mosfet05/Metering_Unit/Kicad/Sub_Ethernet.kicad_sch

## KiCad design Kicad/Sub_Ethernet.kicad_sch (2025-03-12)

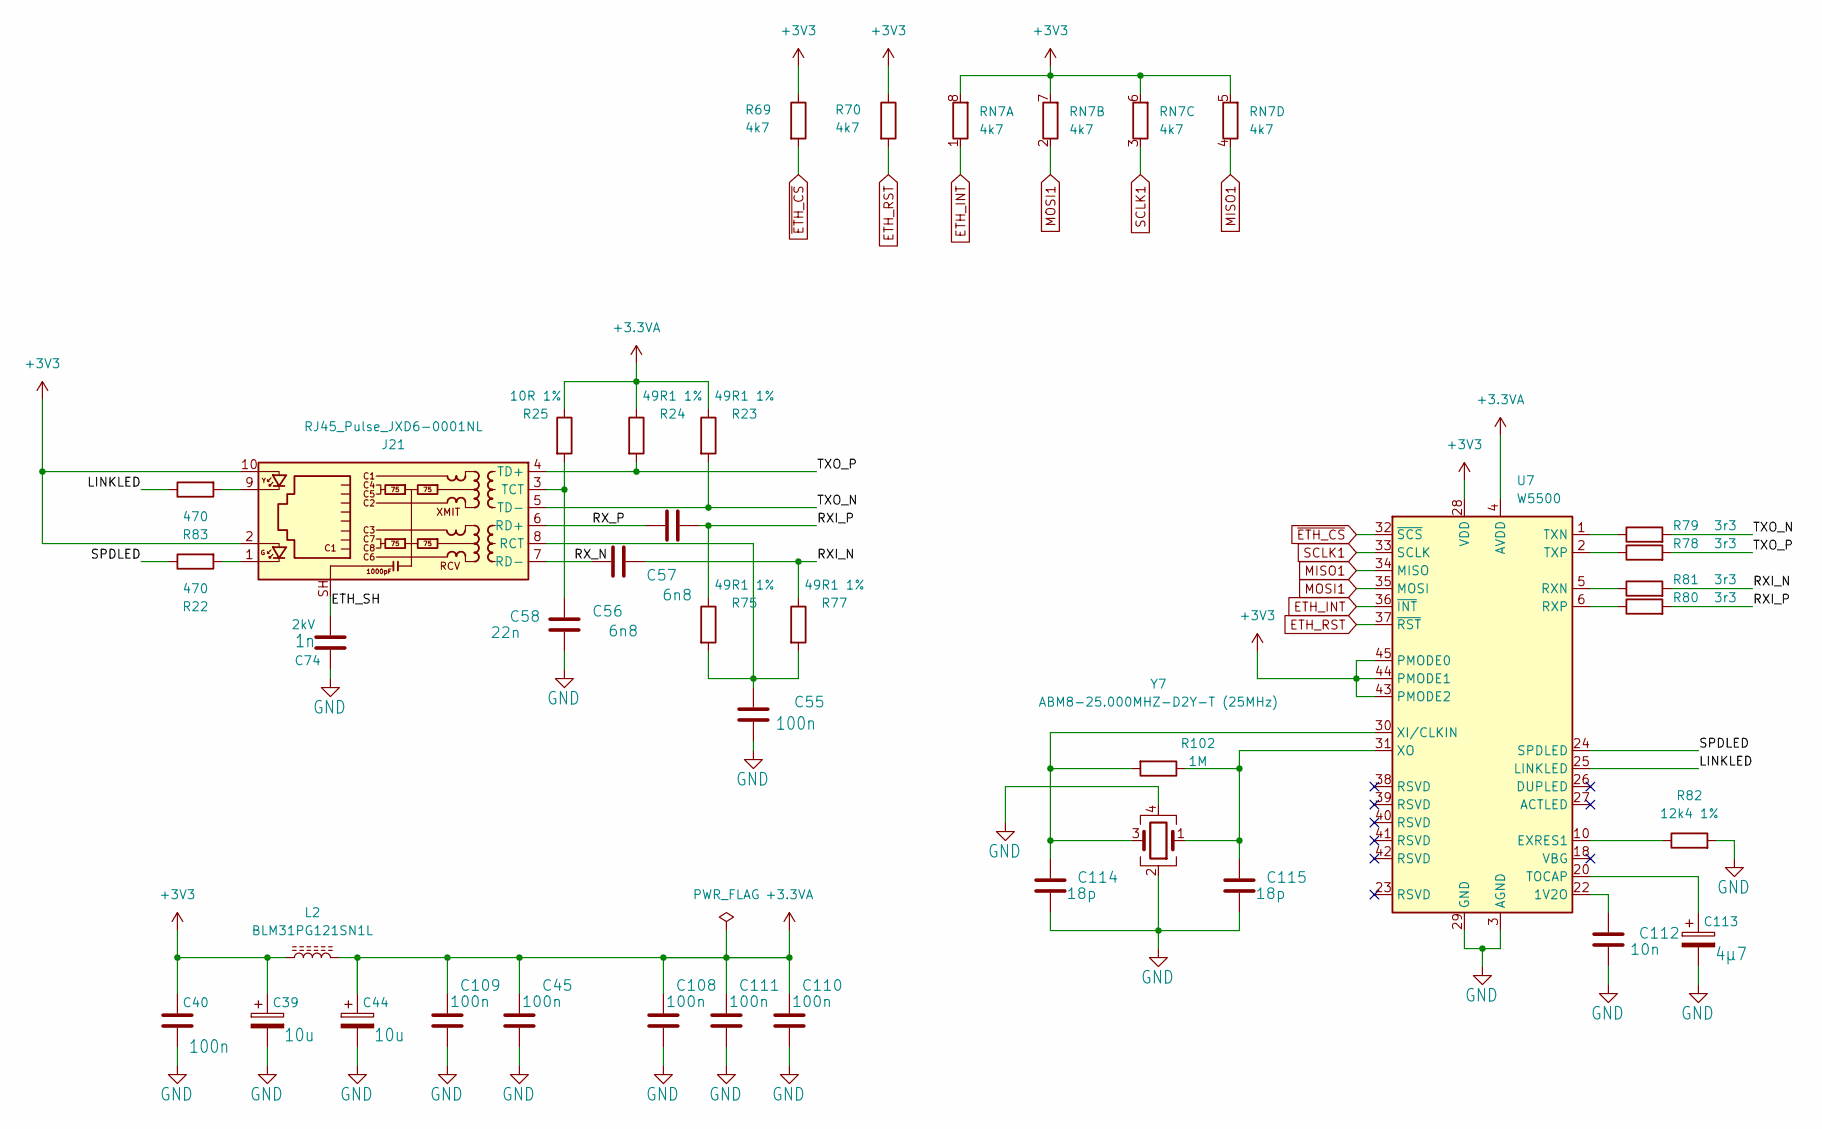
[picture p14: schematic Sub_Ethernet.kicad_sch]

Parts:
C39, C44: 10u; CP_Elec_4x5.3
C40, C55: 100n; C_1210_3225Metric_Pad1.33x2.70mm_HandSolder
C45, C108, C109, C110, C111: 100n; C_0805_2012Metric_Pad1.18x1.45mm_HandSolder
C56, C57: 6n8; C_0805_2012Metric_Pad1.18x1.45mm_HandSolder
C58: 22n; C_0805_2012Metric_Pad1.18x1.45mm_HandSolder
C74: 1n; C_1808_4520Metric_Pad1.72x2.30mm_HandSolder
C112: 10n; C_0805_2012Metric_Pad1.18x1.45mm_HandSolder
C113: 4µ7; CP_Elec_4x5.4
C114, C115: 18p; C_0805_2012Metric_Pad1.18x1.45mm_HandSolder
J21: RJ45_Pulse_JXD6-0001NL; RJ45_Pulse_JXD6-0001NL_Horizontal
L2: BLM31PG121SN1L; L_1206_3216Metric_Pad1.22x1.90mm_HandSolder
R22, R83: 470; R_1210_3225Metric_Pad1.30x2.65mm_HandSolder
R23, R24, R75, R77: 49R1 1%; R_0805_2012Metric_Pad1.20x1.40mm_HandSolder
R25: 10R 1%; R_0805_2012Metric_Pad1.20x1.40mm_HandSolder
R69, R70: 4k7; R_1210_3225Metric_Pad1.30x2.65mm_HandSolder
R78, R79, R80, R81: 3r3; R_0805_2012Metric_Pad1.20x1.40mm_HandSolder
R82: 12k4 1%; R_1210_3225Metric_Pad1.30x2.65mm_HandSolder
R102: 1M; R_0805_2012Metric_Pad1.20x1.40mm_HandSolder
RN7: 4k7; R_Array_Convex_4x1206
U7: W5500; LQFP-48_7x7mm_P0.5mm
Y7: ABM8-25.000MHZ-D2Y-T (25MHz); Crystal_SMD_3225-4Pin_3.2x2.5mm

Connections:
+3.3VA: C44.1, C45.2, C108.2, C109.2, C110.2, C111.2, L2.2, R23.1, R24.1, R25.1, U7.4 (AVDD), U7.8 (AVDD), U7.11 (AVDD), U7.15 (AVDD), U7.17 (AVDD), U7.21 (AVDD)
+3V3: C39.1, C40.1, J21.2, J21.10, L2.1, R69.1, R70.1, RN7.5 (R4.2), RN7.6 (R3.2), RN7.7 (R2.2), RN7.8 (R1.2), U7.28 (VDD), U7.43 (PMODE2), U7.44 (PMODE1), U7.45 (PMODE0)
ETH_INT: RN7.1 (R1.1), U7.36 (~INT)
ETH_RST: R70.2, U7.37 (~RST)
ETH_SH: C74.1, J21.SH
GND: C39.2, C40.2, C44.2, C45.1, C55.1, C58.1, C74.2, C108.1, C109.1, C110.1, C111.1, C112.1, C113.2, C114.1, C115.1, R82.2, U7.3 (AGND), U7.9 (AGND), U7.14 (AGND), U7.16 (AGND), U7.19 (AGND), U7.29 (GND), U7.48 (AGND), Y7.2, Y7.4
LINKLED: R83.1, U7.25 (LINKLED)
MISO1: RN7.4 (R4.1), U7.34 (MISO)
MOSI1: RN7.2 (R2.1), U7.35 (MOSI)
unnamed: C55.2, J21.8 (RCT), R75.2, R77.2
unnamed: C58.2, J21.3 (TCT), R25.2
unnamed: C112.2, U7.22 (1V2O)
unnamed: C113.1, U7.20 (TOCAP)
unnamed: C114.2, R102.2, U7.30 (XI/CLKIN), Y7.3
unnamed: C115.2, R102.1, U7.31 (XO), Y7.1
unnamed: J21.1, R22.2
unnamed: J21.9, R83.2
unnamed: R78.1, U7.2 (TXP)
unnamed: R79.1, U7.1 (TXN)
unnamed: R80.1, U7.6 (RXP)
unnamed: R81.1, U7.5 (RXN)
unnamed: R82.1, U7.10 (EXRES1)
RXI_N: C56.1, R77.1, R81.2
RXI_P: C57.1, R75.1, R80.2
RX_N: C56.2, J21.7 (RD-)
RX_P: C57.2, J21.6 (RD+)
SCLK1: RN7.3 (R3.1), U7.33 (SCLK)
SPDLED: R22.1, U7.24 (SPDLED)
TXO_N: J21.5 (TD-), R23.2, R79.2
TXO_P: J21.4 (TD+), R24.2, R78.2
~ETH_CS: R69.2, U7.32 (~SCS)
