mosfet05/Metering_Unit/Kicad/Sub_IHM.kicad_sch

## KiCad design Kicad/Sub_IHM.kicad_sch (2025-03-12)

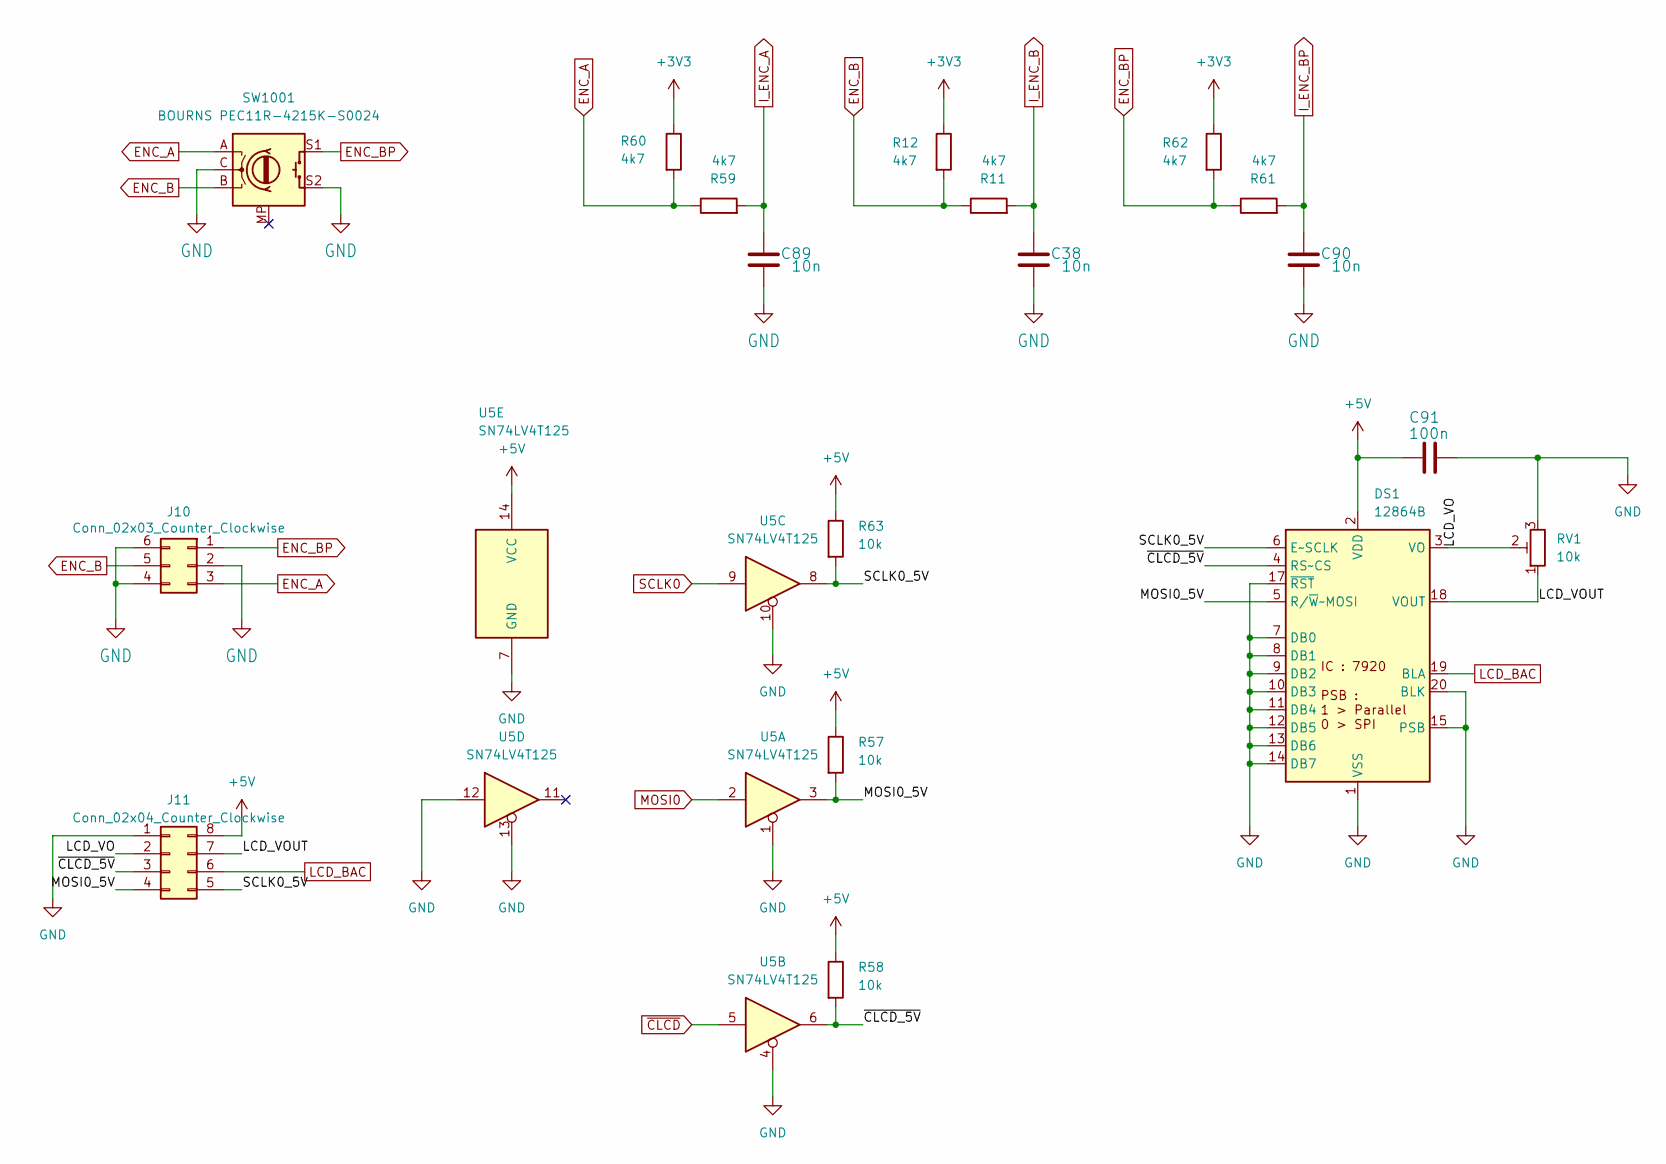
[picture p15: schematic Sub_IHM.kicad_sch]

Parts:
C38, C89, C90: 10n; C_1812_4532Metric_Pad1.57x3.40mm_HandSolder
C91: 100n; C_1812_4532Metric_Pad1.57x3.40mm_HandSolder
DS1: 12864B; GraphicLCD_12864B_WithoutPads
J10: Conn_02x03_Counter_Clockwise; IDC-Header_2x03_P2.54mm_Vertical
J11: Conn_02x04_Counter_Clockwise; IDC-Header_2x04_P2.54mm_Vertical
R11, R12, R59, R60, R61, R62: 4k7; R_1210_3225Metric_Pad1.30x2.65mm_HandSolder
R57, R58, R63: 10k; R_1210_3225Metric_Pad1.30x2.65mm_HandSolder
RV1: 10k; Potentiometer_Piher_T-16H_Single_Horizontal
SW1001: BOURNS PEC11R-4215K-S0024
U5: SN74LV4T125; TSSOP-14_4.4x5mm_P0.65mm

Connections:
+3V3: R12.1, R60.1, R62.1
+5V: C91.1, DS1.2 (VDD), J11.8, R57.1, R58.1, R63.1, U5.14 (VCC)
ENC_A: J10.3, R59.1, R60.2, SW1001.A
ENC_B: J10.5, R11.1, R12.2, SW1001.B
ENC_BP: J10.1, R61.1, R62.2, SW1001.S1
GND: C38.2, C89.2, C90.2, C91.2, DS1.1 (VSS), DS1.7 (DB0), DS1.8 (DB1), DS1.9 (DB2), DS1.10 (DB3), DS1.11 (DB4), DS1.12 (DB5), DS1.13 (DB6), DS1.14 (DB7), DS1.15 (PSB), DS1.17 (~RST), DS1.20 (BLK), J10.2, J10.4, J10.6, J11.1, RV1.3, SW1001.C, SW1001.S2, U5.1, U5.4, U5.7 (GND), U5.10, U5.12, U5.13
I_ENC_A: C89.1, R59.2
I_ENC_B: C38.1, R11.2
I_ENC_BP: C90.1, R61.2
LCD_BAC: DS1.19 (BLA), J11.6
LCD_VO: DS1.3 (VO), J11.2, RV1.2
LCD_VOUT: DS1.18 (NC), J11.7, RV1.1
MOSI0: U5.2
MOSI0_5V: DS1.5 (R/~W~MOSI), J11.4, R57.2, U5.3
SCLK0: U5.9
SCLK0_5V: DS1.6 (E~SCLK), J11.5, R63.2, U5.8
~CLCD_5V: DS1.4 (RS~CS), J11.3, R58.2, U5.6
~CLCD: U5.5
