mosfet05/Metering_Unit/Kicad/Sub_Mes_01.kicad_sch

## KiCad design Kicad/Sub_Mes_01.kicad_sch (2025-03-12)

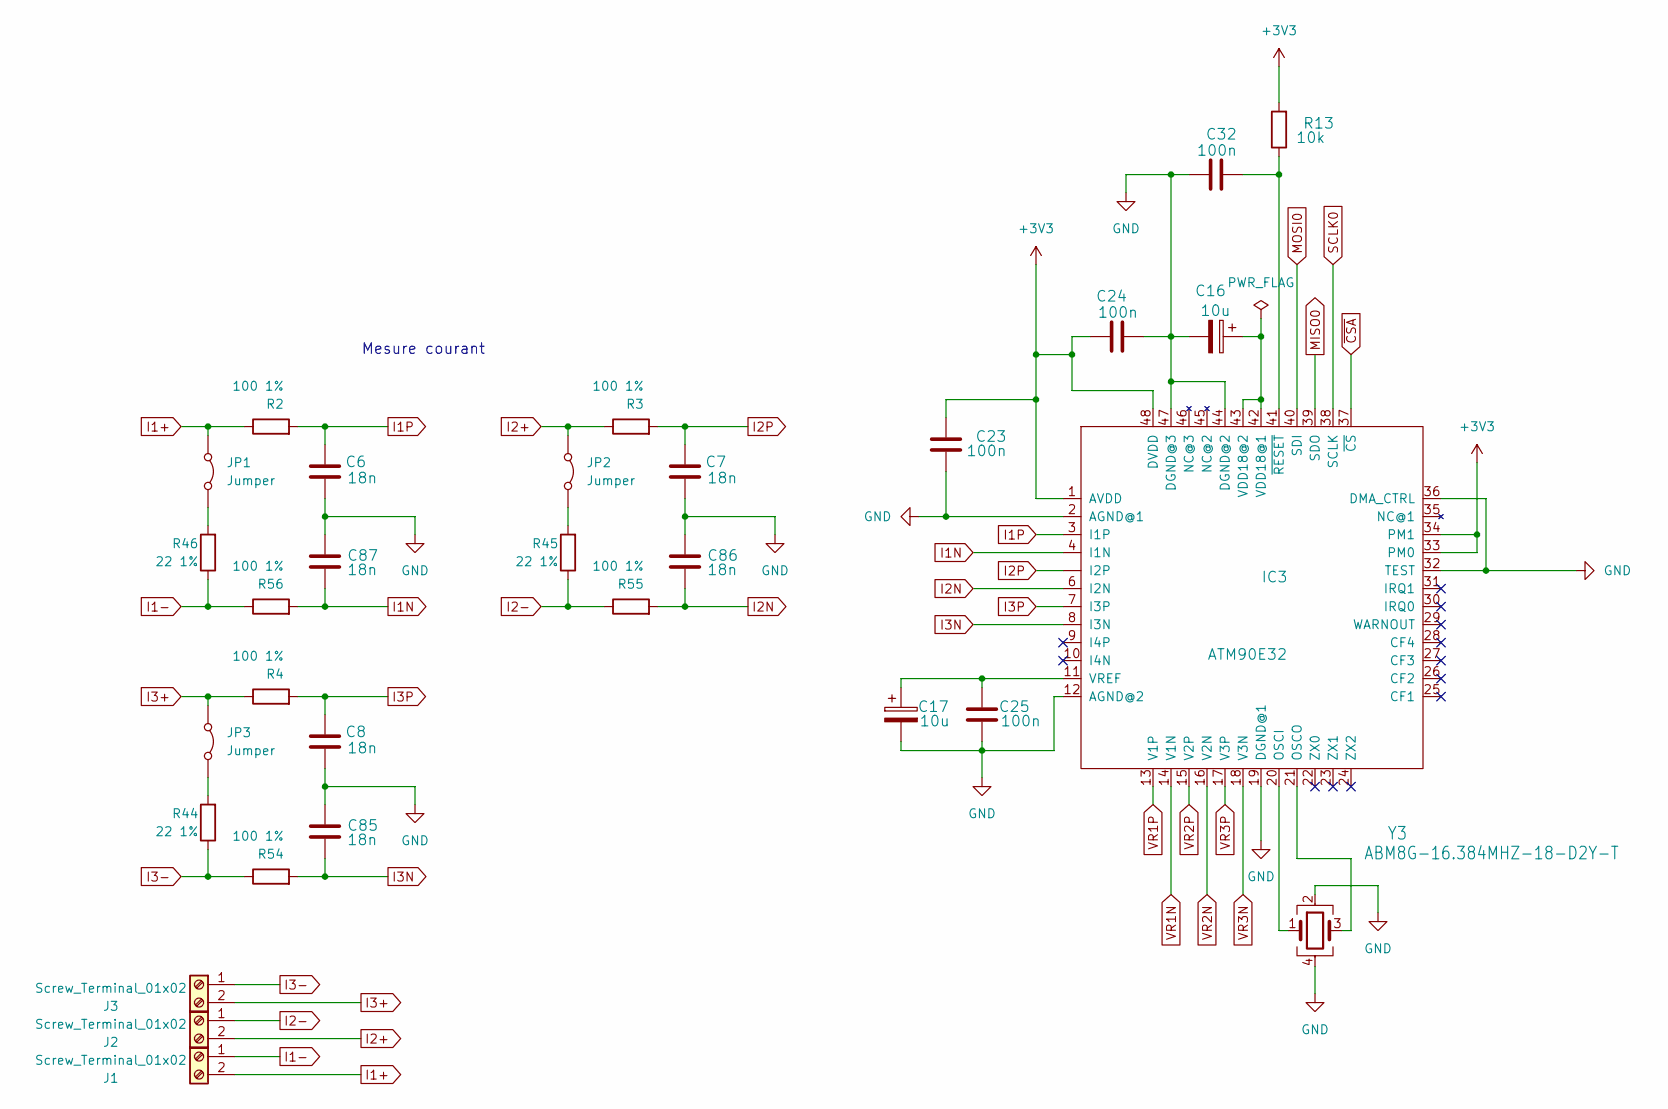
[picture p16: schematic Sub_Mes_01.kicad_sch]

Parts:
C6, C7, C8, C85, C86, C87: 18n; C_0805_2012Metric_Pad1.18x1.45mm_HandSolder
C16, C17: 10u; CP_Elec_4x5.3
C23, C24, C25, C32: 100n; C_1812_4532Metric_Pad1.57x3.40mm_HandSolder
IC3: ATM90E32; TQFP-48_7x7mm_P0.5mm
J1, J2, J3: Screw_Terminal_01x02; TerminalBlock_VN_1x02_P2.54mm_Horizontal
JP1, JP2, JP3: Jumper; PinHeader_1x02_P2.54mm_Vertical
R2, R3, R4, R54, R55, R56: 100 1%; R_1210_3225Metric_Pad1.30x2.65mm_HandSolder
R13: 10k; R_1210_3225Metric_Pad1.30x2.65mm_HandSolder
R44, R45, R46: 22 1%; R_1210_3225Metric_Pad1.30x2.65mm_HandSolder
Y3: ABM8G-16.384MHZ-18-D2Y-T; Crystal_SMD_3225-4Pin_3.2x2.5mm

Connections:
+3V3: C23.2, C24.2, IC3.1 (AVDD), IC3.33 (PM0), IC3.34 (PM1), IC3.48 (DVDD), R13.2
GND: C6.2, C7.2, C8.2, C16.2, C17.2, C23.1, C24.1, C25.2, C32.2, C85.1, C86.1, C87.1, IC3.2 (AGND@1), IC3.12 (AGND@2), IC3.19 (DGND@1), IC3.32 (TEST), IC3.36 (DMA_CTRL), IC3.44 (DGND@2), IC3.47 (DGND@3), Y3.2, Y3.4
I1+: J1.2, JP1.1 (A), R2.1
I1-: J1.1, R46.1, R56.1
I1N: C87.2, IC3.4 (I1N), R56.2
I1P: C6.1, IC3.3 (I1P), R2.2
I2+: J2.2, JP2.1 (A), R3.1
I2-: J2.1, R45.1, R55.1
I2N: C86.2, IC3.6 (I2N), R55.2
I2P: C7.1, IC3.5 (I2P), R3.2
I3+: J3.2, JP3.1 (A), R4.1
I3-: J3.1, R44.1, R54.1
I3N: C85.2, IC3.8 (I3N), R54.2
I3P: C8.1, IC3.7 (I3P), R4.2
MISO0: IC3.39 (SDO)
MOSI0: IC3.40 (SDI)
unnamed: C16.1, IC3.42 (VDD18@1), IC3.43 (VDD18@2)
unnamed: C17.1, C25.1, IC3.11 (VREF)
unnamed: C32.1, IC3.41 (~RESET), R13.1
unnamed: IC3.20 (OSCI), Y3.1
unnamed: IC3.21 (OSCO), Y3.3
unnamed: JP1.2 (B), R46.2
unnamed: JP2.2 (B), R45.2
unnamed: JP3.2 (B), R44.2
SCLK0: IC3.38 (SCLK)
VR1N: IC3.14 (V1N)
VR1P: IC3.13 (V1P)
VR2N: IC3.16 (V2N)
VR2P: IC3.15 (V2P)
VR3N: IC3.18 (V3N)
VR3P: IC3.17 (V3P)
~CSA: IC3.37 (~CS)

Notes on the sheet:
Mesure courant
