mosfet05/Metering_Unit/Kicad/Sub_Mes_02.kicad_sch

## KiCad design Kicad/Sub_Mes_02.kicad_sch (2025-03-12)

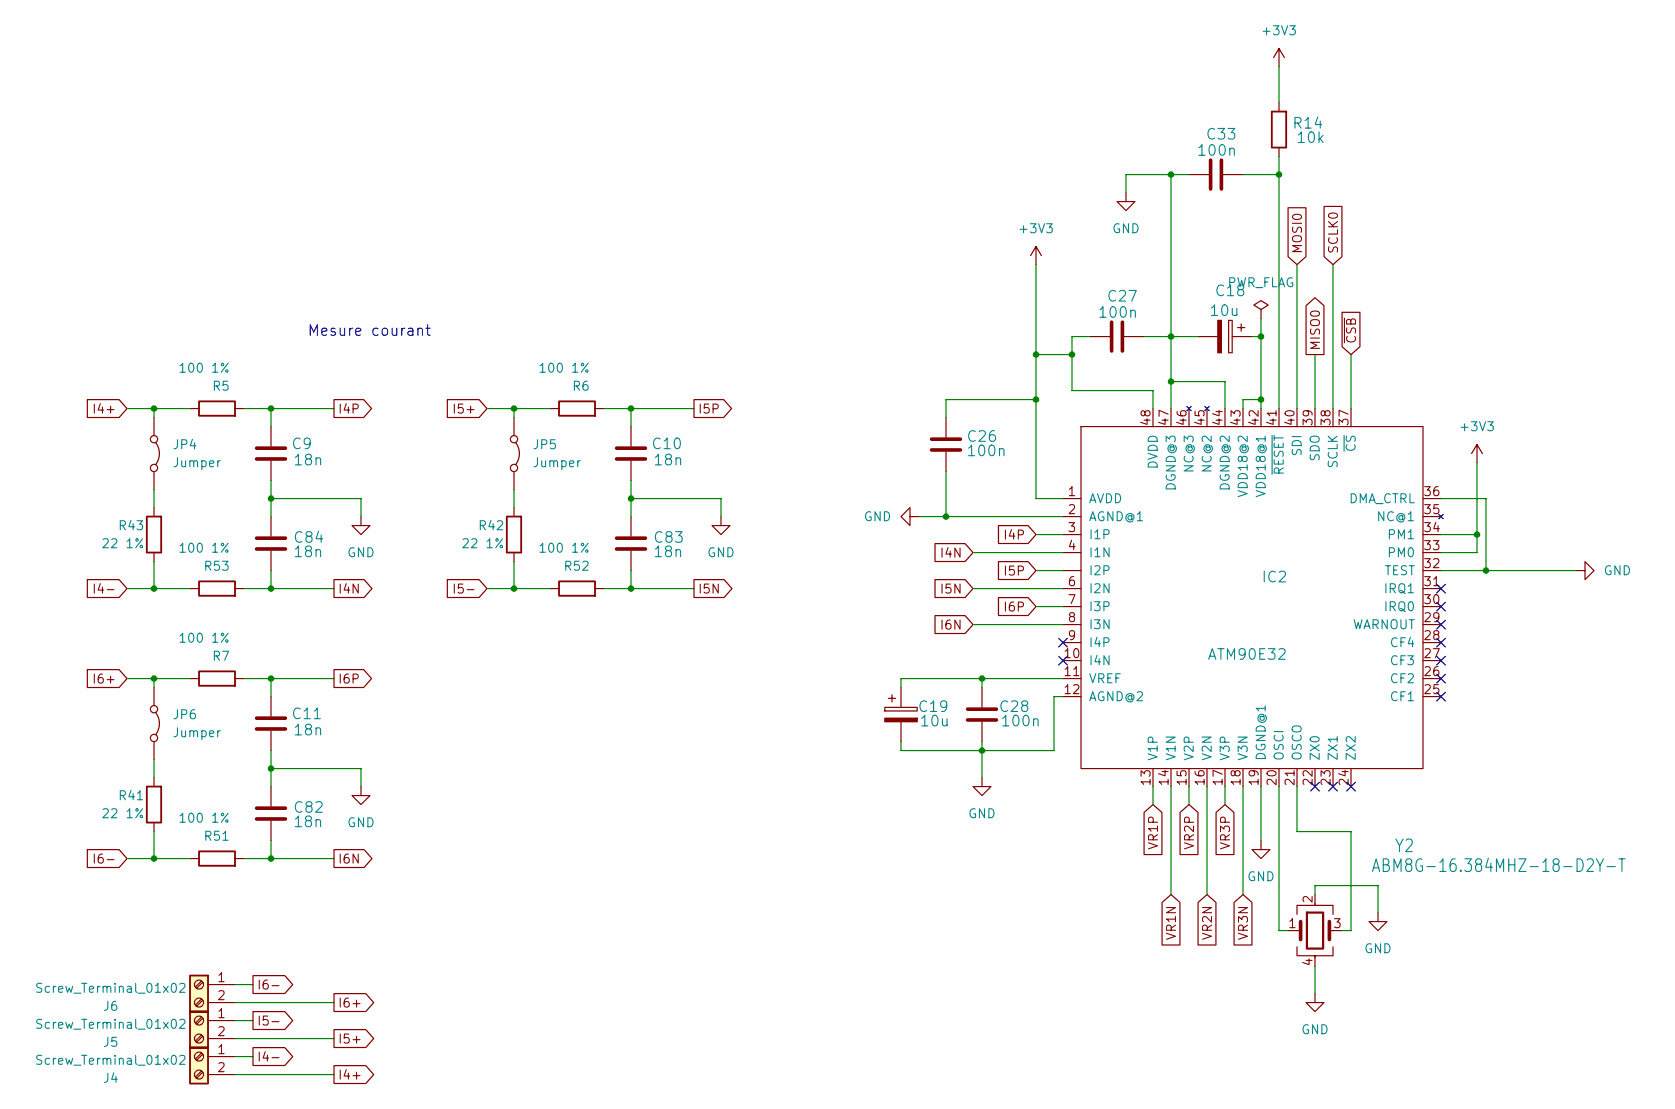
[picture p17: schematic Sub_Mes_02.kicad_sch]

Parts:
C9, C10, C11, C82, C83, C84: 18n; C_0805_2012Metric_Pad1.18x1.45mm_HandSolder
C18, C19: 10u; CP_Elec_4x5.3
C26, C27, C28, C33: 100n; C_1812_4532Metric_Pad1.57x3.40mm_HandSolder
IC2: ATM90E32; TQFP-48_7x7mm_P0.5mm
J4, J5, J6: Screw_Terminal_01x02; TerminalBlock_VN_1x02_P2.54mm_Horizontal
JP4, JP5, JP6: Jumper; PinHeader_1x02_P2.54mm_Vertical
R5, R6, R7, R51, R52, R53: 100 1%; R_1210_3225Metric_Pad1.30x2.65mm_HandSolder
R14: 10k; R_1210_3225Metric_Pad1.30x2.65mm_HandSolder
R41, R42, R43: 22 1%; R_1210_3225Metric_Pad1.30x2.65mm_HandSolder
Y2: ABM8G-16.384MHZ-18-D2Y-T; Crystal_SMD_3225-4Pin_3.2x2.5mm

Connections:
+3V3: C26.2, C27.2, IC2.1 (AVDD), IC2.33 (PM0), IC2.34 (PM1), IC2.48 (DVDD), R14.2
GND: C9.2, C10.2, C11.2, C18.2, C19.2, C26.1, C27.1, C28.2, C33.2, C82.1, C83.1, C84.1, IC2.2 (AGND@1), IC2.12 (AGND@2), IC2.19 (DGND@1), IC2.32 (TEST), IC2.36 (DMA_CTRL), IC2.44 (DGND@2), IC2.47 (DGND@3), Y2.2, Y2.4
I4+: J4.2, JP4.1 (A), R5.1
I4-: J4.1, R43.1, R53.1
I4N: C84.2, IC2.4 (I1N), R53.2
I4P: C9.1, IC2.3 (I1P), R5.2
I5+: J5.2, JP5.1 (A), R6.1
I5-: J5.1, R42.1, R52.1
I5N: C83.2, IC2.6 (I2N), R52.2
I5P: C10.1, IC2.5 (I2P), R6.2
I6+: J6.2, JP6.1 (A), R7.1
I6-: J6.1, R41.1, R51.1
I6N: C82.2, IC2.8 (I3N), R51.2
I6P: C11.1, IC2.7 (I3P), R7.2
MISO0: IC2.39 (SDO)
MOSI0: IC2.40 (SDI)
unnamed: C18.1, IC2.42 (VDD18@1), IC2.43 (VDD18@2)
unnamed: C19.1, C28.1, IC2.11 (VREF)
unnamed: C33.1, IC2.41 (~RESET), R14.1
unnamed: IC2.20 (OSCI), Y2.1
unnamed: IC2.21 (OSCO), Y2.3
unnamed: JP4.2 (B), R43.2
unnamed: JP5.2 (B), R42.2
unnamed: JP6.2 (B), R41.2
SCLK0: IC2.38 (SCLK)
VR1N: IC2.14 (V1N)
VR1P: IC2.13 (V1P)
VR2N: IC2.16 (V2N)
VR2P: IC2.15 (V2P)
VR3N: IC2.18 (V3N)
VR3P: IC2.17 (V3P)
~CSB: IC2.37 (~CS)

Notes on the sheet:
Mesure courant
