mosfet05/Metering_Unit/Kicad/Sub_Mes_03.kicad_sch

## KiCad design Kicad/Sub_Mes_03.kicad_sch (2025-03-12)

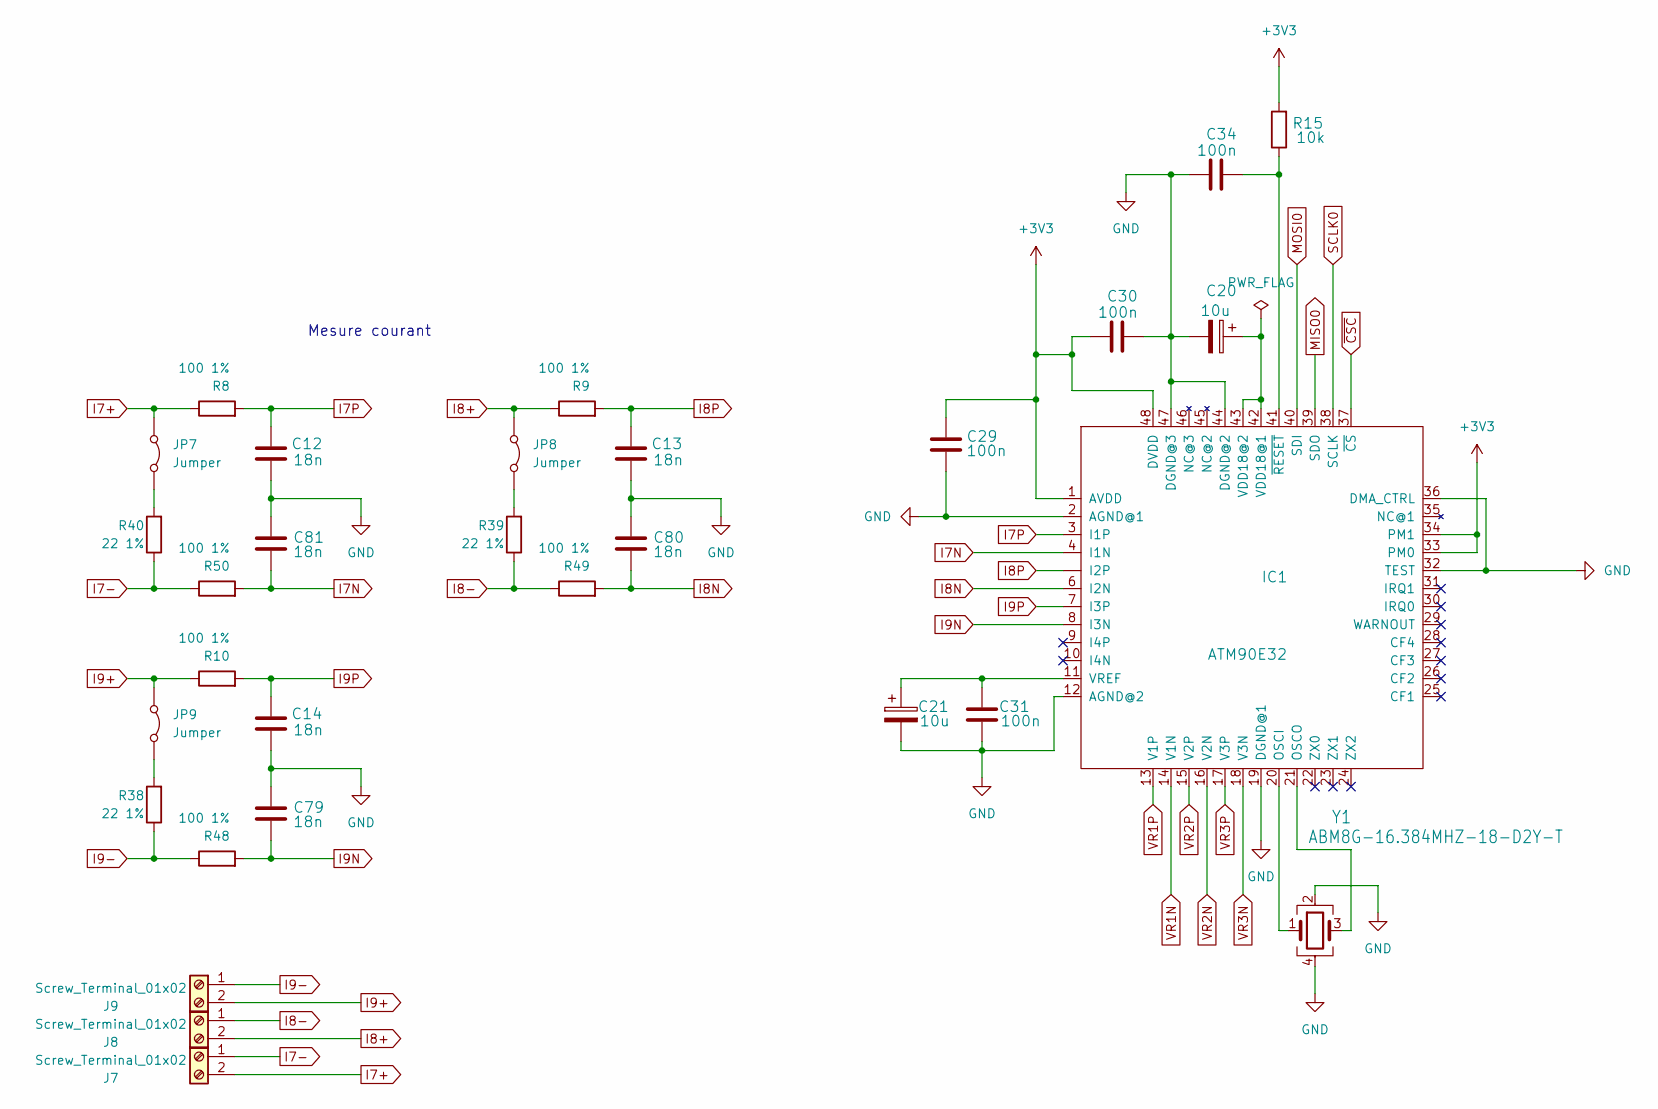
[picture p18: schematic Sub_Mes_03.kicad_sch]

Parts:
C12, C13, C14, C79, C80, C81: 18n; C_0805_2012Metric_Pad1.18x1.45mm_HandSolder
C20, C21: 10u; CP_Elec_4x5.3
C29, C30, C31, C34: 100n; C_1812_4532Metric_Pad1.57x3.40mm_HandSolder
IC1: ATM90E32; TQFP-48_7x7mm_P0.5mm
J7, J8, J9: Screw_Terminal_01x02; TerminalBlock_VN_1x02_P2.54mm_Horizontal
JP7, JP8, JP9: Jumper; PinHeader_1x02_P2.54mm_Vertical
R8, R9, R10, R48, R49, R50: 100 1%; R_1210_3225Metric_Pad1.30x2.65mm_HandSolder
R15: 10k; R_1210_3225Metric_Pad1.30x2.65mm_HandSolder
R38, R39, R40: 22 1%; R_1210_3225Metric_Pad1.30x2.65mm_HandSolder
Y1: ABM8G-16.384MHZ-18-D2Y-T; Crystal_SMD_3225-4Pin_3.2x2.5mm

Connections:
+3V3: C29.2, C30.2, IC1.1 (AVDD), IC1.33 (PM0), IC1.34 (PM1), IC1.48 (DVDD), R15.2
GND: C12.2, C13.2, C14.2, C20.2, C21.2, C29.1, C30.1, C31.2, C34.2, C79.1, C80.1, C81.1, IC1.2 (AGND@1), IC1.12 (AGND@2), IC1.19 (DGND@1), IC1.32 (TEST), IC1.36 (DMA_CTRL), IC1.44 (DGND@2), IC1.47 (DGND@3), Y1.2, Y1.4
I7+: J7.2, JP7.1 (A), R8.1
I7-: J7.1, R40.1, R50.1
I7N: C81.2, IC1.4 (I1N), R50.2
I7P: C12.1, IC1.3 (I1P), R8.2
I8+: J8.2, JP8.1 (A), R9.1
I8-: J8.1, R39.1, R49.1
I8N: C80.2, IC1.6 (I2N), R49.2
I8P: C13.1, IC1.5 (I2P), R9.2
I9+: J9.2, JP9.1 (A), R10.1
I9-: J9.1, R38.1, R48.1
I9N: C79.2, IC1.8 (I3N), R48.2
I9P: C14.1, IC1.7 (I3P), R10.2
MISO0: IC1.39 (SDO)
MOSI0: IC1.40 (SDI)
unnamed: C20.1, IC1.42 (VDD18@1), IC1.43 (VDD18@2)
unnamed: C21.1, C31.1, IC1.11 (VREF)
unnamed: C34.1, IC1.41 (~RESET), R15.1
unnamed: IC1.20 (OSCI), Y1.1
unnamed: IC1.21 (OSCO), Y1.3
unnamed: JP7.2 (B), R40.2
unnamed: JP8.2 (B), R39.2
unnamed: JP9.2 (B), R38.2
SCLK0: IC1.38 (SCLK)
VR1N: IC1.14 (V1N)
VR1P: IC1.13 (V1P)
VR2N: IC1.16 (V2N)
VR2P: IC1.15 (V2P)
VR3N: IC1.18 (V3N)
VR3P: IC1.17 (V3P)
~CSC: IC1.37 (~CS)

Notes on the sheet:
Mesure courant
