mosfet05/Metering_Unit/Kicad/Sub_Mes_04.kicad_sch

## KiCad design Kicad/Sub_Mes_04.kicad_sch (2025-03-12)

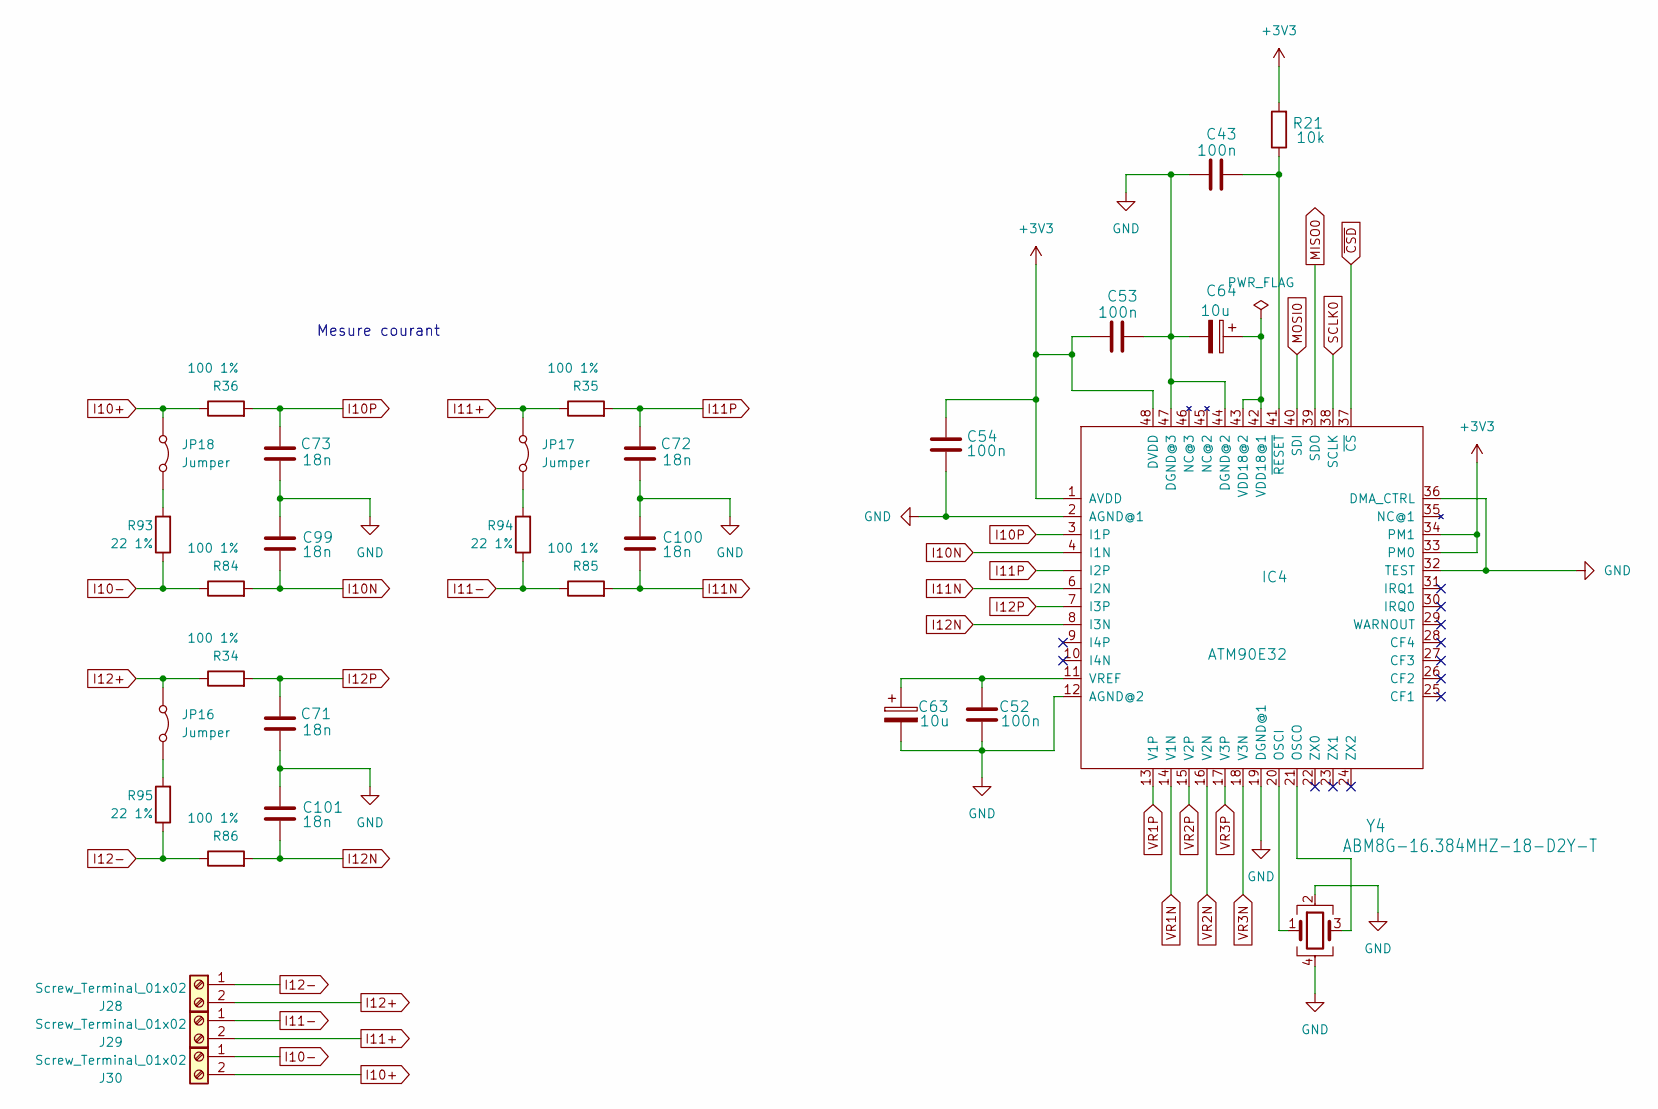
[picture p19: schematic Sub_Mes_04.kicad_sch]

Parts:
C43, C52, C53, C54: 100n; C_1812_4532Metric_Pad1.57x3.40mm_HandSolder
C63, C64: 10u; CP_Elec_4x5.3
C71, C72, C73, C99, C100, C101: 18n; C_0805_2012Metric_Pad1.18x1.45mm_HandSolder
IC4: ATM90E32; TQFP-48_7x7mm_P0.5mm
J28, J29, J30: Screw_Terminal_01x02; TerminalBlock_VN_1x02_P2.54mm_Horizontal
JP16, JP17, JP18: Jumper; PinHeader_1x02_P2.54mm_Vertical
R21: 10k; R_1210_3225Metric_Pad1.30x2.65mm_HandSolder
R34, R35, R36, R84, R85, R86: 100 1%; R_1210_3225Metric_Pad1.30x2.65mm_HandSolder
R93, R94, R95: 22 1%; R_1210_3225Metric_Pad1.30x2.65mm_HandSolder
Y4: ABM8G-16.384MHZ-18-D2Y-T; Crystal_SMD_3225-4Pin_3.2x2.5mm

Connections:
+3V3: C53.2, C54.2, IC4.1 (AVDD), IC4.33 (PM0), IC4.34 (PM1), IC4.48 (DVDD), R21.2
GND: C43.2, C52.2, C53.1, C54.1, C63.2, C64.2, C71.2, C72.2, C73.2, C99.1, C100.1, C101.1, IC4.2 (AGND@1), IC4.12 (AGND@2), IC4.19 (DGND@1), IC4.32 (TEST), IC4.36 (DMA_CTRL), IC4.44 (DGND@2), IC4.47 (DGND@3), Y4.2, Y4.4
I10+: J30.2, JP18.1 (A), R36.1
I10-: J30.1, R84.1, R93.1
I10N: C99.2, IC4.4 (I1N), R84.2
I10P: C73.1, IC4.3 (I1P), R36.2
I11+: J29.2, JP17.1 (A), R35.1
I11-: J29.1, R85.1, R94.1
I11N: C100.2, IC4.6 (I2N), R85.2
I11P: C72.1, IC4.5 (I2P), R35.2
I12+: J28.2, JP16.1 (A), R34.1
I12-: J28.1, R86.1, R95.1
I12N: C101.2, IC4.8 (I3N), R86.2
I12P: C71.1, IC4.7 (I3P), R34.2
MISO0: IC4.39 (SDO)
MOSI0: IC4.40 (SDI)
unnamed: C43.1, IC4.41 (~RESET), R21.1
unnamed: C52.1, C63.1, IC4.11 (VREF)
unnamed: C64.1, IC4.42 (VDD18@1), IC4.43 (VDD18@2)
unnamed: IC4.20 (OSCI), Y4.1
unnamed: IC4.21 (OSCO), Y4.3
unnamed: JP16.2 (B), R95.2
unnamed: JP17.2 (B), R94.2
unnamed: JP18.2 (B), R93.2
SCLK0: IC4.38 (SCLK)
VR1N: IC4.14 (V1N)
VR1P: IC4.13 (V1P)
VR2N: IC4.16 (V2N)
VR2P: IC4.15 (V2P)
VR3N: IC4.18 (V3N)
VR3P: IC4.17 (V3P)
~CSD: IC4.37 (~CS)

Notes on the sheet:
Mesure courant
