mosfet05/Metering_Unit/Kicad/Sub_Mes_05.kicad_sch

## KiCad design Kicad/Sub_Mes_05.kicad_sch (2025-03-12)

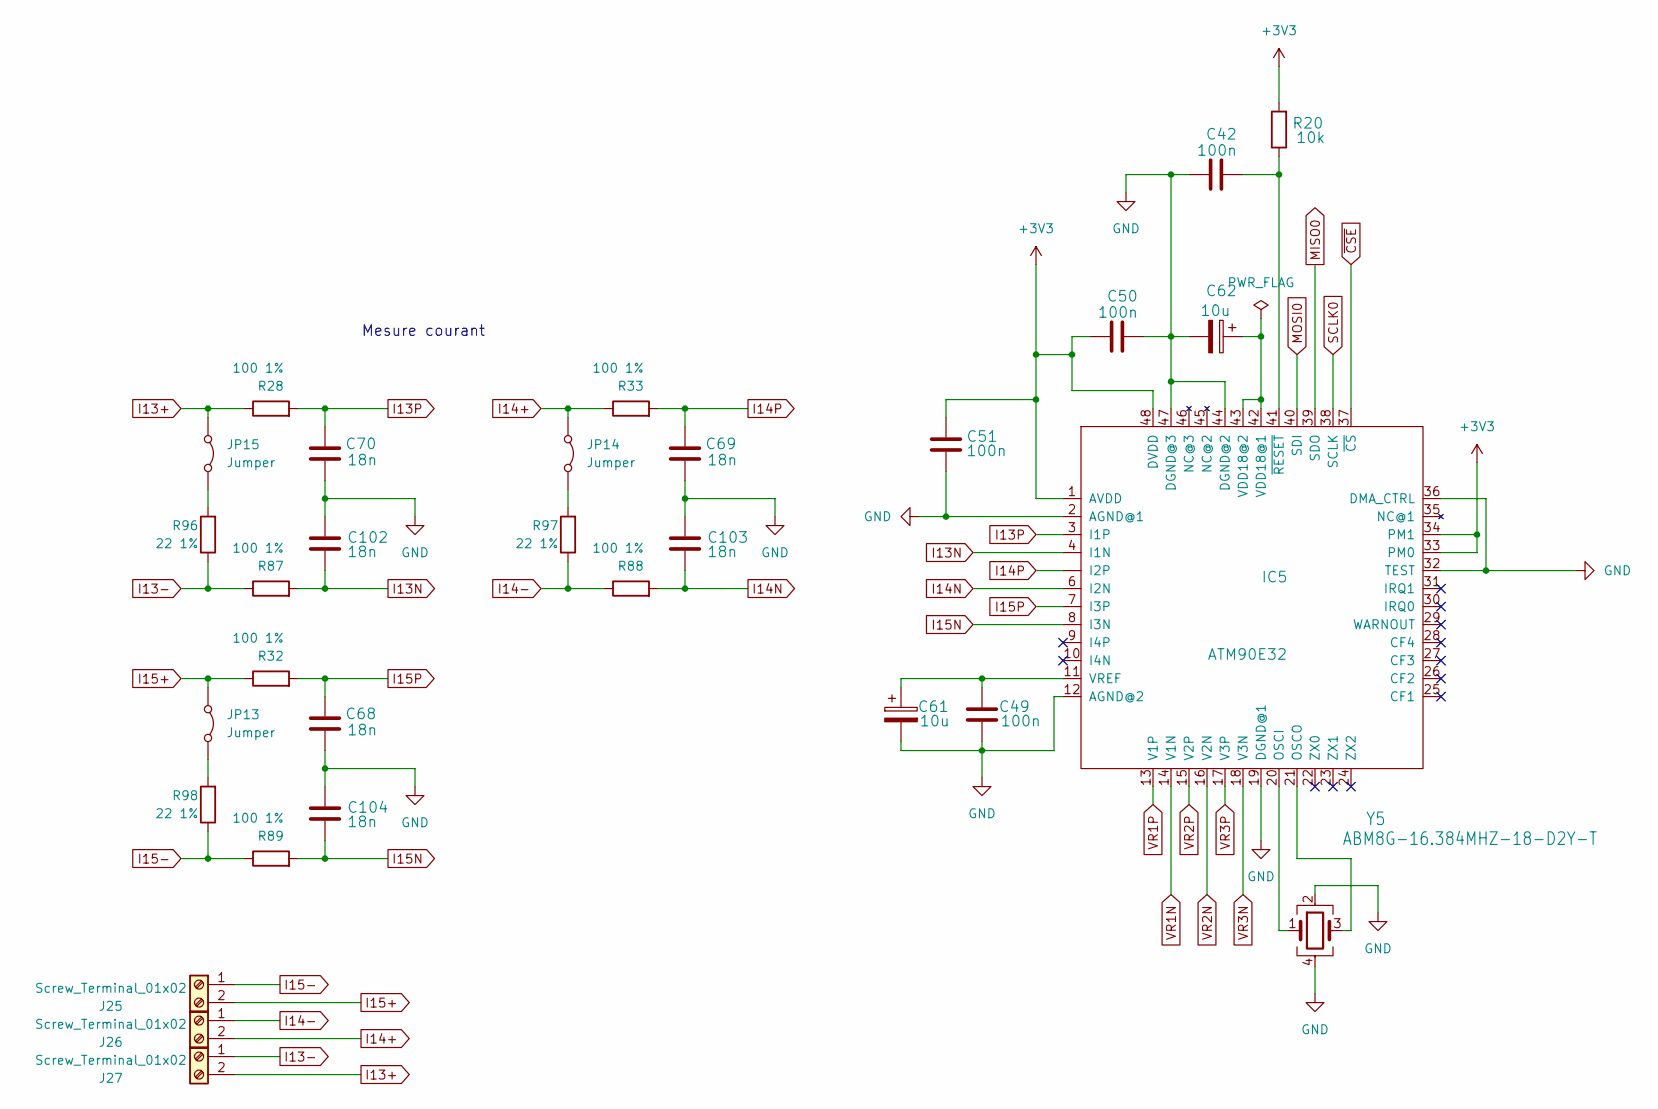
[picture p20: schematic Sub_Mes_05.kicad_sch]

Parts:
C42, C49, C50, C51: 100n; C_1812_4532Metric_Pad1.57x3.40mm_HandSolder
C61, C62: 10u; CP_Elec_4x5.3
C68, C69, C70, C102, C103, C104: 18n; C_0805_2012Metric_Pad1.18x1.45mm_HandSolder
IC5: ATM90E32; TQFP-48_7x7mm_P0.5mm
J25, J26, J27: Screw_Terminal_01x02; TerminalBlock_VN_1x02_P2.54mm_Horizontal
JP13, JP14, JP15: Jumper; PinHeader_1x02_P2.54mm_Vertical
R20: 10k; R_1210_3225Metric_Pad1.30x2.65mm_HandSolder
R28, R32, R33, R87, R88, R89: 100 1%; R_1210_3225Metric_Pad1.30x2.65mm_HandSolder
R96, R97, R98: 22 1%; R_1210_3225Metric_Pad1.30x2.65mm_HandSolder
Y5: ABM8G-16.384MHZ-18-D2Y-T; Crystal_SMD_3225-4Pin_3.2x2.5mm

Connections:
+3V3: C50.2, C51.2, IC5.1 (AVDD), IC5.33 (PM0), IC5.34 (PM1), IC5.48 (DVDD), R20.2
GND: C42.2, C49.2, C50.1, C51.1, C61.2, C62.2, C68.2, C69.2, C70.2, C102.1, C103.1, C104.1, IC5.2 (AGND@1), IC5.12 (AGND@2), IC5.19 (DGND@1), IC5.32 (TEST), IC5.36 (DMA_CTRL), IC5.44 (DGND@2), IC5.47 (DGND@3), Y5.2, Y5.4
I13+: J27.2, JP15.1 (A), R28.1
I13-: J27.1, R87.1, R96.1
I13N: C102.2, IC5.4 (I1N), R87.2
I13P: C70.1, IC5.3 (I1P), R28.2
I14+: J26.2, JP14.1 (A), R33.1
I14-: J26.1, R88.1, R97.1
I14N: C103.2, IC5.6 (I2N), R88.2
I14P: C69.1, IC5.5 (I2P), R33.2
I15+: J25.2, JP13.1 (A), R32.1
I15-: J25.1, R89.1, R98.1
I15N: C104.2, IC5.8 (I3N), R89.2
I15P: C68.1, IC5.7 (I3P), R32.2
MISO0: IC5.39 (SDO)
MOSI0: IC5.40 (SDI)
unnamed: C42.1, IC5.41 (~RESET), R20.1
unnamed: C49.1, C61.1, IC5.11 (VREF)
unnamed: C62.1, IC5.42 (VDD18@1), IC5.43 (VDD18@2)
unnamed: IC5.20 (OSCI), Y5.1
unnamed: IC5.21 (OSCO), Y5.3
unnamed: JP13.2 (B), R98.2
unnamed: JP14.2 (B), R97.2
unnamed: JP15.2 (B), R96.2
SCLK0: IC5.38 (SCLK)
VR1N: IC5.14 (V1N)
VR1P: IC5.13 (V1P)
VR2N: IC5.16 (V2N)
VR2P: IC5.15 (V2P)
VR3N: IC5.18 (V3N)
VR3P: IC5.17 (V3P)
~CSE: IC5.37 (~CS)

Notes on the sheet:
Mesure courant
