mosfet05/Metering_Unit/Kicad/Sub_Mes_06.kicad_sch

## KiCad design Kicad/Sub_Mes_06.kicad_sch (2025-03-12)

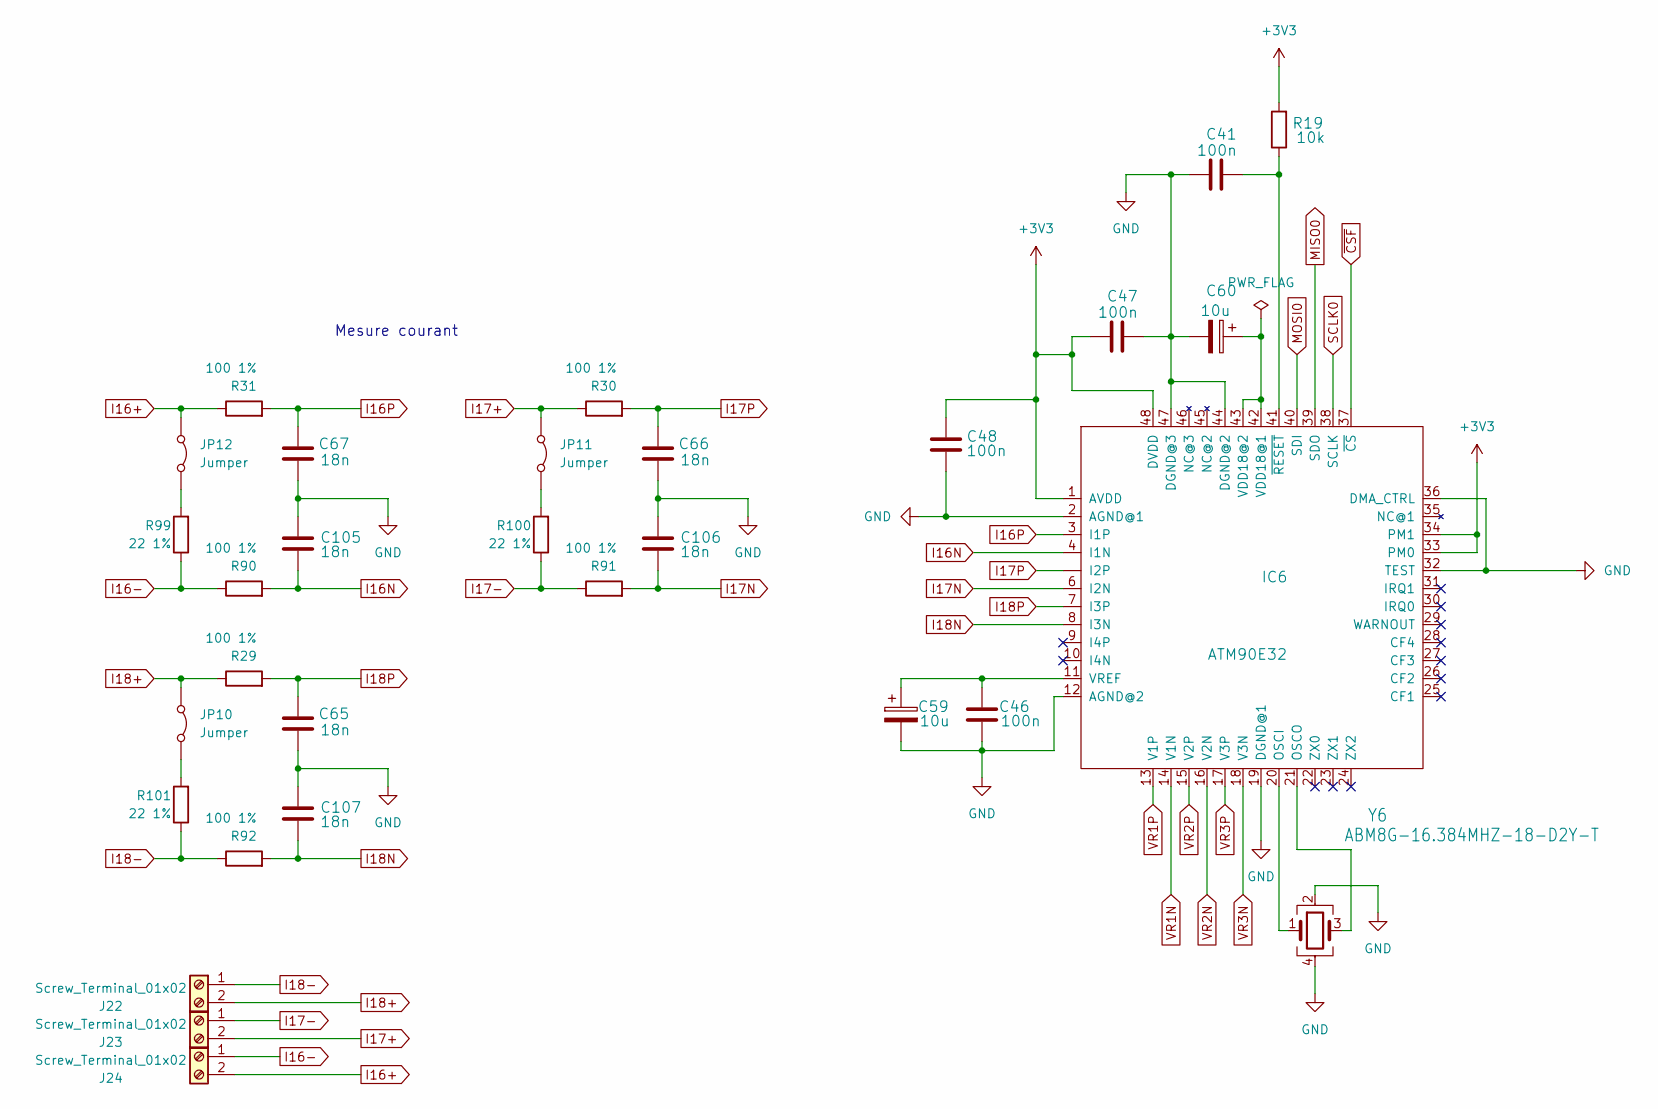
[picture p21: schematic Sub_Mes_06.kicad_sch]

Parts:
C41, C46, C47, C48: 100n; C_1812_4532Metric_Pad1.57x3.40mm_HandSolder
C59, C60: 10u; CP_Elec_4x5.3
C65, C66, C67, C105, C106, C107: 18n; C_0805_2012Metric_Pad1.18x1.45mm_HandSolder
IC6: ATM90E32; TQFP-48_7x7mm_P0.5mm
J22, J23, J24: Screw_Terminal_01x02; TerminalBlock_VN_1x02_P2.54mm_Horizontal
JP10, JP11, JP12: Jumper; PinHeader_1x02_P2.54mm_Vertical
R19: 10k; R_1210_3225Metric_Pad1.30x2.65mm_HandSolder
R29, R30, R31, R90, R91, R92: 100 1%; R_1210_3225Metric_Pad1.30x2.65mm_HandSolder
R99, R100, R101: 22 1%; R_1210_3225Metric_Pad1.30x2.65mm_HandSolder
Y6: ABM8G-16.384MHZ-18-D2Y-T; Crystal_SMD_3225-4Pin_3.2x2.5mm

Connections:
+3V3: C47.2, C48.2, IC6.1 (AVDD), IC6.33 (PM0), IC6.34 (PM1), IC6.48 (DVDD), R19.2
GND: C41.2, C46.2, C47.1, C48.1, C59.2, C60.2, C65.2, C66.2, C67.2, C105.1, C106.1, C107.1, IC6.2 (AGND@1), IC6.12 (AGND@2), IC6.19 (DGND@1), IC6.32 (TEST), IC6.36 (DMA_CTRL), IC6.44 (DGND@2), IC6.47 (DGND@3), Y6.2, Y6.4
I16+: J24.2, JP12.1 (A), R31.1
I16-: J24.1, R90.1, R99.1
I16N: C105.2, IC6.4 (I1N), R90.2
I16P: C67.1, IC6.3 (I1P), R31.2
I17+: J23.2, JP11.1 (A), R30.1
I17-: J23.1, R91.1, R100.1
I17N: C106.2, IC6.6 (I2N), R91.2
I17P: C66.1, IC6.5 (I2P), R30.2
I18+: J22.2, JP10.1 (A), R29.1
I18-: J22.1, R92.1, R101.1
I18N: C107.2, IC6.8 (I3N), R92.2
I18P: C65.1, IC6.7 (I3P), R29.2
MISO0: IC6.39 (SDO)
MOSI0: IC6.40 (SDI)
unnamed: C41.1, IC6.41 (~RESET), R19.1
unnamed: C46.1, C59.1, IC6.11 (VREF)
unnamed: C60.1, IC6.42 (VDD18@1), IC6.43 (VDD18@2)
unnamed: IC6.20 (OSCI), Y6.1
unnamed: IC6.21 (OSCO), Y6.3
unnamed: JP10.2 (B), R101.2
unnamed: JP11.2 (B), R100.2
unnamed: JP12.2 (B), R99.2
SCLK0: IC6.38 (SCLK)
VR1N: IC6.14 (V1N)
VR1P: IC6.13 (V1P)
VR2N: IC6.16 (V2N)
VR2P: IC6.15 (V2P)
VR3N: IC6.18 (V3N)
VR3P: IC6.17 (V3P)
~CSF: IC6.37 (~CS)

Notes on the sheet:
Mesure courant
