mosfet05/Metering_Unit/Kicad/Sub_Mes_07.kicad_sch

## KiCad design Kicad/Sub_Mes_07.kicad_sch (2025-03-12)

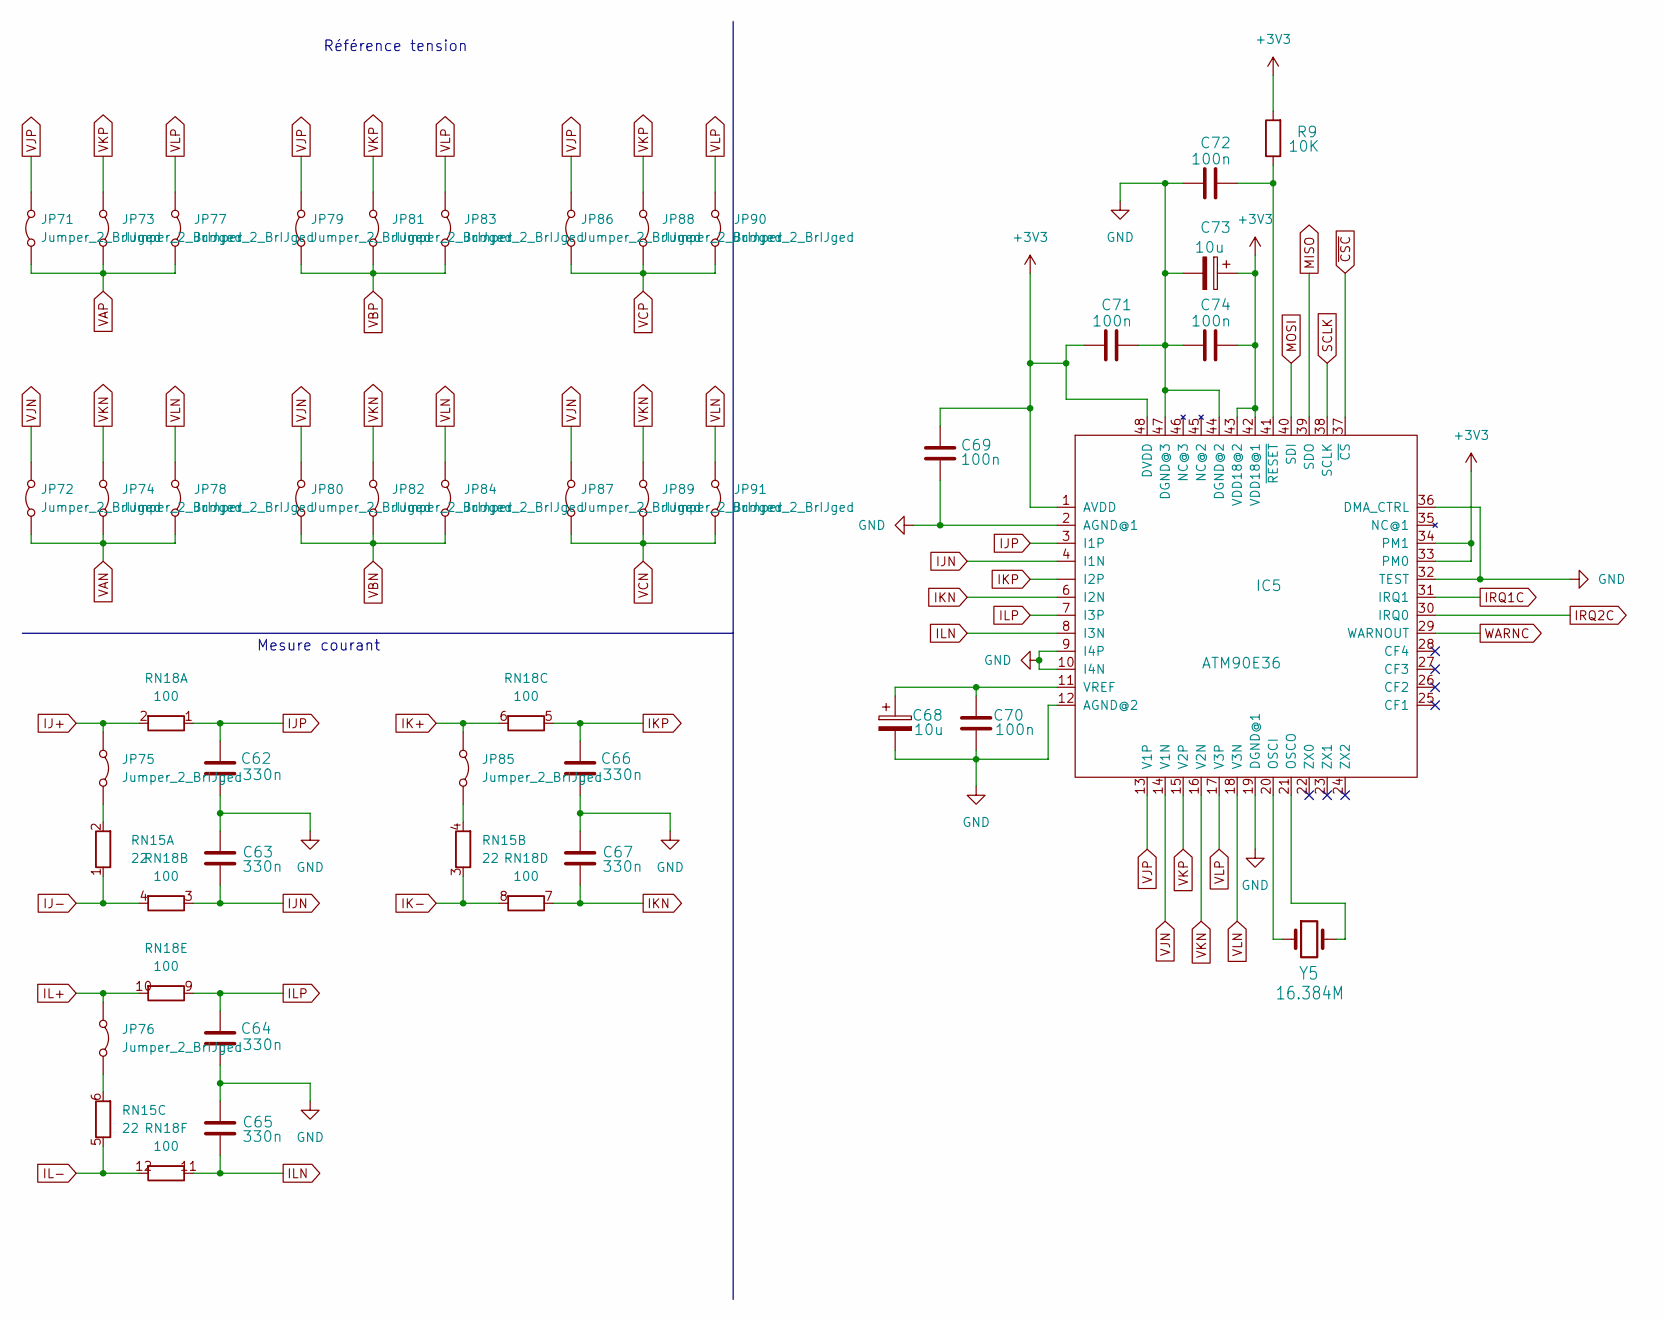
[picture p22: schematic Sub_Mes_07.kicad_sch]

Parts:
C62, C63, C64, C65, C66, C67: 330n; C_1812_4532Metric_Pad1.57x3.40mm_HandSolder
C68, C73: 10u; CP_Elec_3x5.3
C69, C70, C71, C72, C74: 100n; C_1812_4532Metric_Pad1.57x3.40mm_HandSolder
IC5: ATM90E36; PinSocket_1x02_P2.54mm_Vertical
JP71, JP72, JP73, JP74, JP75, JP76, JP77, JP78, JP79, JP80, JP81, JP82, JP83, JP84, JP85, JP86, JP87, JP88, JP89, JP90, JP91: Jumper_2_BrIJged; PinSocket_1x02_P2.54mm_Vertical
R9: 10K; R_1812_4532Metric_Pad1.30x3.40mm_HandSolder
RN15: 22; R_Array_SIP6
RN18: 100; R_Array_SIP12
Y5: 16.384M; Crystal_SMD_HC49-SD_HandSoldering

Connections:
+3V3: C69.2, C71.2, C73.1, C74.1, IC5.1 (AVDD), IC5.33 (PM0), IC5.34 (PM1), IC5.42 (VDD18@1), IC5.43 (VDD18@2), IC5.48 (DVDD), R9.2
GND: C62.2, C63.1, C64.2, C65.1, C66.2, C67.1, C68.2, C69.1, C70.2, C71.1, C72.2, C73.2, C74.2, IC5.2 (AGND@1), IC5.9 (I4P), IC5.10 (I4N), IC5.12 (AGND@2), IC5.19 (DGND@1), IC5.32 (TEST), IC5.36 (DMA_CTRL), IC5.44 (DGND@2), IC5.47 (DGND@3)
IJ+: JP75.1 (A), RN18.2 (R1.2)
IJ-: RN15.1 (R1.1), RN18.4 (R2.2)
IJN: C63.2, IC5.4 (I1N), RN18.3 (R2.1)
IJP: C62.1, IC5.3 (I1P), RN18.1 (R1.1)
IK+: JP85.1 (A), RN18.6 (R3.2)
IK-: RN15.3 (R2.1), RN18.8 (R4.2)
IKN: C67.2, IC5.6 (I2N), RN18.7 (R4.1)
IKP: C66.1, IC5.5 (I2P), RN18.5 (R3.1)
IL+: JP76.1 (A), RN18.10 (R5.2)
IL-: RN15.5 (R3.1), RN18.12 (R6.2)
ILN: C65.2, IC5.8 (I3N), RN18.11 (R6.1)
ILP: C64.1, IC5.7 (I3P), RN18.9 (R5.1)
IRQ1C: IC5.31 (IRQ1)
IRQ2C: IC5.30 (IRQ0)
MISO: IC5.39 (SDO)
MOSI: IC5.40 (SDI)
unnamed: C68.1, C70.1, IC5.11 (VREF)
unnamed: C72.1, IC5.41 (~RESET), R9.1
unnamed: IC5.20 (OSCI), Y5.1
unnamed: IC5.21 (OSCO), Y5.2
unnamed: JP75.2 (B), RN15.2 (R1.2)
unnamed: JP76.2 (B), RN15.6 (R3.2)
unnamed: JP85.2 (B), RN15.4 (R2.2)
SCLK: IC5.38 (SCLK)
VAN: JP72.1 (A), JP74.2 (B), JP78.2 (B)
VAP: JP71.1 (A), JP73.2 (B), JP77.2 (B)
VBN: JP80.1 (A), JP82.2 (B), JP84.2 (B)
VBP: JP79.1 (A), JP81.2 (B), JP83.2 (B)
VCN: JP87.1 (A), JP89.2 (B), JP91.2 (B)
VCP: JP86.1 (A), JP88.2 (B), JP90.2 (B)
VJN: IC5.14 (V1N), JP72.2 (B), JP80.2 (B), JP87.2 (B)
VJP: IC5.13 (V1P), JP71.2 (B), JP79.2 (B), JP86.2 (B)
VKN: IC5.16 (V2N), JP74.1 (A), JP82.1 (A), JP89.1 (A)
VKP: IC5.15 (V2P), JP73.1 (A), JP81.1 (A), JP88.1 (A)
VLN: IC5.18 (V3N), JP78.1 (A), JP84.1 (A), JP91.1 (A)
VLP: IC5.17 (V3P), JP77.1 (A), JP83.1 (A), JP90.1 (A)
WARNC: IC5.29 (WARNOUT)
~CSC: IC5.37 (~CS)

Notes on the sheet:
Référence tension
Mesure courant
