mosfet05/Metering_Unit/Kicad/Sub_Mes_08.kicad_sch

## KiCad design Kicad/Sub_Mes_08.kicad_sch (2025-03-12)

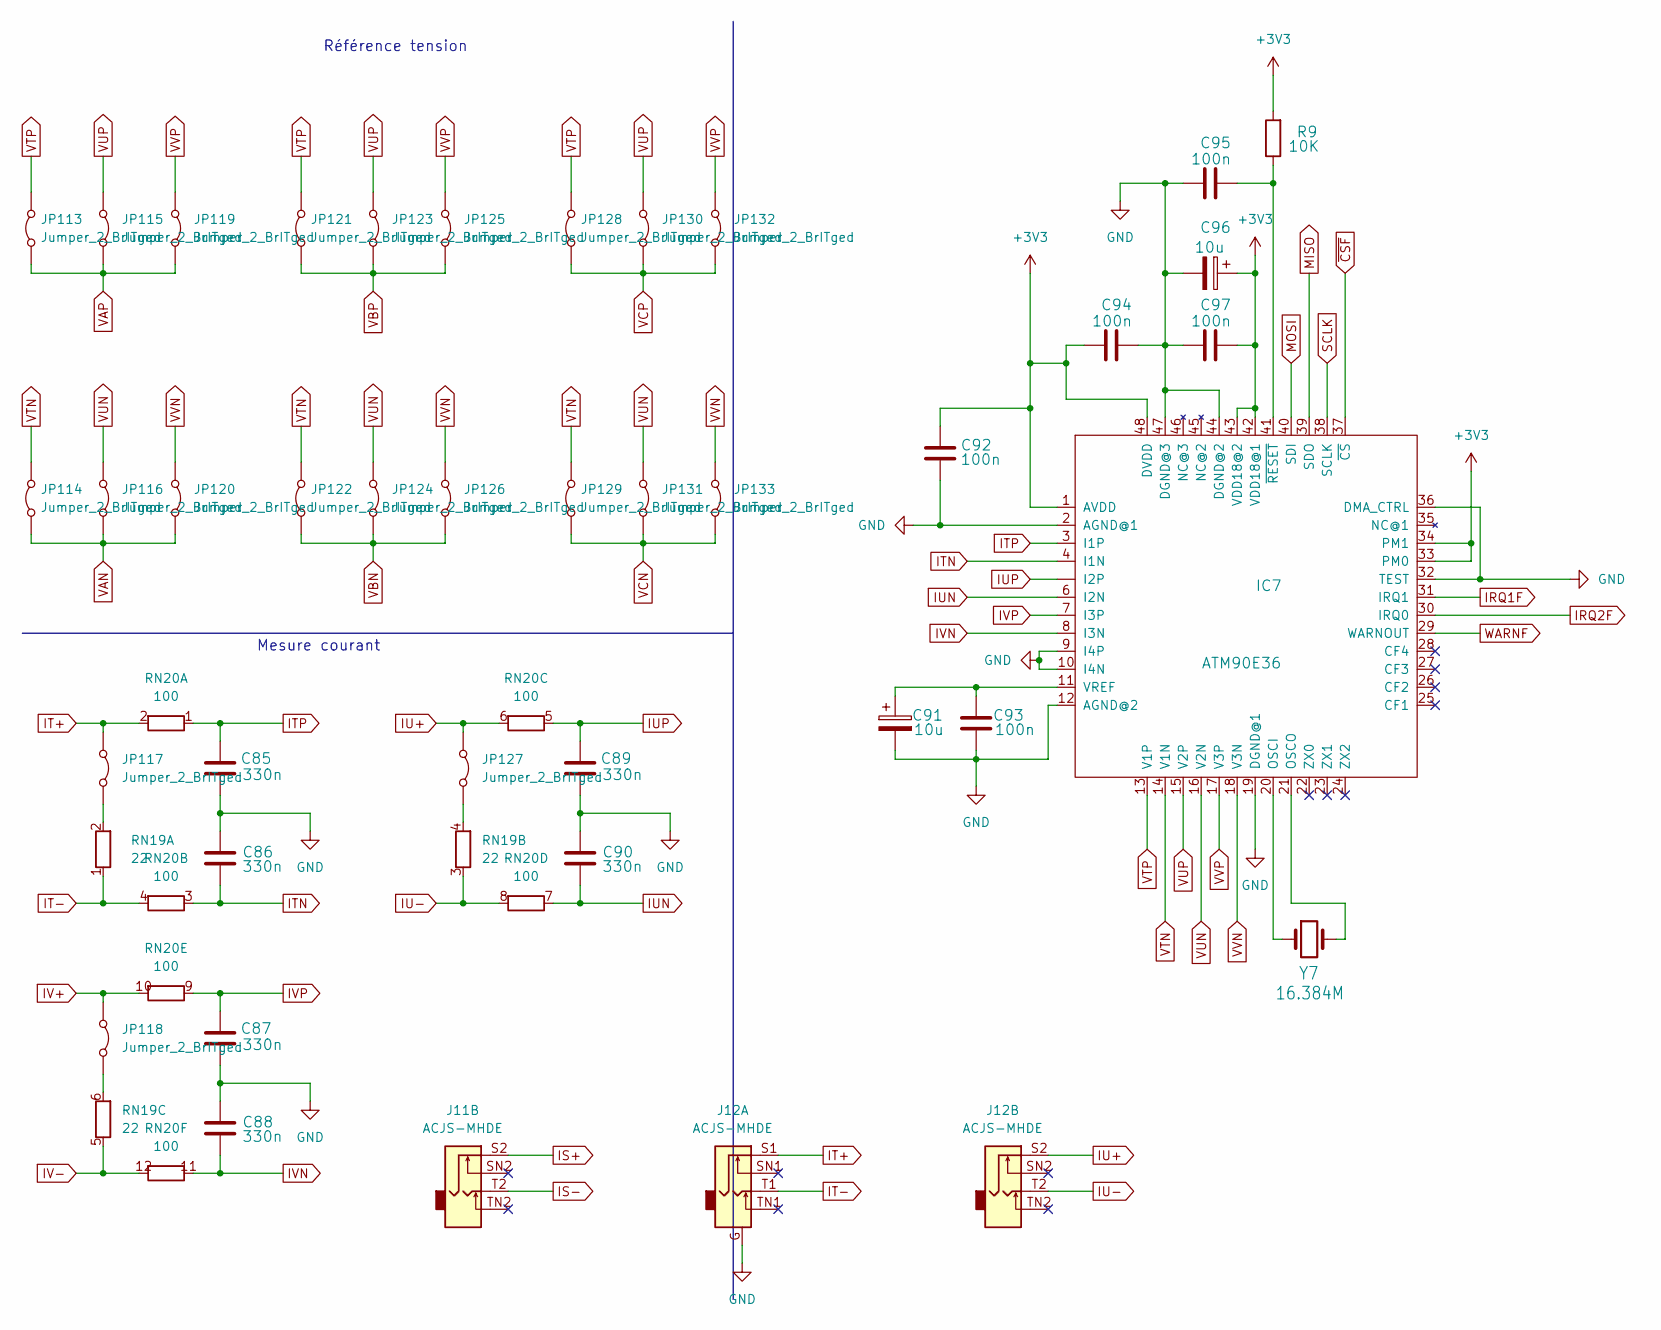
[picture p23: schematic Sub_Mes_08.kicad_sch]

Parts:
C85, C86, C87, C88, C89, C90: 330n; C_1812_4532Metric_Pad1.57x3.40mm_HandSolder
C91, C96: 10u; CP_Elec_3x5.3
C92, C93, C94, C95, C97: 100n; C_1812_4532Metric_Pad1.57x3.40mm_HandSolder
IC7: ATM90E36; TQFP-48_7x7mm_P0.5mm
J11, J12: ACJS-MHDE; PinSocket_1x02_P2.54mm_Vertical
JP113, JP114, JP115, JP116, JP117, JP118, JP119, JP120, JP121, JP122, JP123, JP124, JP125, JP126, JP127, JP128, JP129, JP130, JP131, JP132, JP133: Jumper_2_BrITged; PinSocket_1x02_P2.54mm_Vertical
R9: 10K; R_1210_3225Metric_Pad1.30x2.65mm_HandSolder
RN19: 22; R_Array_SIP6
RN20: 100; R_Array_SIP12
Y7: 16.384M; Crystal_SMD_HC49-SD_HandSoldering

Connections:
+3V3: C92.2, C94.2, C96.1, C97.1, IC7.1 (AVDD), IC7.33 (PM0), IC7.34 (PM1), IC7.42 (VDD18@1), IC7.43 (VDD18@2), IC7.48 (DVDD), R9.2
GND: C85.2, C86.1, C87.2, C88.1, C89.2, C90.1, C91.2, C92.1, C93.2, C94.1, C95.2, C96.2, C97.2, IC7.2 (AGND@1), IC7.9 (I4P), IC7.10 (I4N), IC7.12 (AGND@2), IC7.19 (DGND@1), IC7.32 (TEST), IC7.36 (DMA_CTRL), IC7.44 (DGND@2), IC7.47 (DGND@3), J12.G
IRQ1F: IC7.31 (IRQ1)
IRQ2F: IC7.30 (IRQ0)
IS+: J11.S2
IS-: J11.T2
IT+: J12.S1, JP117.1 (A), RN20.2 (R1.2)
IT-: J12.T1, RN19.1 (R1.1), RN20.4 (R2.2)
ITN: C86.2, IC7.4 (I1N), RN20.3 (R2.1)
ITP: C85.1, IC7.3 (I1P), RN20.1 (R1.1)
IU+: J12.S2, JP127.1 (A), RN20.6 (R3.2)
IU-: J12.T2, RN19.3 (R2.1), RN20.8 (R4.2)
IUN: C90.2, IC7.6 (I2N), RN20.7 (R4.1)
IUP: C89.1, IC7.5 (I2P), RN20.5 (R3.1)
IV+: JP118.1 (A), RN20.10 (R5.2)
IV-: RN19.5 (R3.1), RN20.12 (R6.2)
IVN: C88.2, IC7.8 (I3N), RN20.11 (R6.1)
IVP: C87.1, IC7.7 (I3P), RN20.9 (R5.1)
MISO: IC7.39 (SDO)
MOSI: IC7.40 (SDI)
unnamed: C91.1, C93.1, IC7.11 (VREF)
unnamed: C95.1, IC7.41 (~RESET), R9.1
unnamed: IC7.20 (OSCI), Y7.1
unnamed: IC7.21 (OSCO), Y7.2
unnamed: JP117.2 (B), RN19.2 (R1.2)
unnamed: JP118.2 (B), RN19.6 (R3.2)
unnamed: JP127.2 (B), RN19.4 (R2.2)
SCLK: IC7.38 (SCLK)
VAN: JP114.1 (A), JP116.2 (B), JP120.2 (B)
VAP: JP113.1 (A), JP115.2 (B), JP119.2 (B)
VBN: JP122.1 (A), JP124.2 (B), JP126.2 (B)
VBP: JP121.1 (A), JP123.2 (B), JP125.2 (B)
VCN: JP129.1 (A), JP131.2 (B), JP133.2 (B)
VCP: JP128.1 (A), JP130.2 (B), JP132.2 (B)
VTN: IC7.14 (V1N), JP114.2 (B), JP122.2 (B), JP129.2 (B)
VTP: IC7.13 (V1P), JP113.2 (B), JP121.2 (B), JP128.2 (B)
VUN: IC7.16 (V2N), JP116.1 (A), JP124.1 (A), JP131.1 (A)
VUP: IC7.15 (V2P), JP115.1 (A), JP123.1 (A), JP130.1 (A)
VVN: IC7.18 (V3N), JP120.1 (A), JP126.1 (A), JP133.1 (A)
VVP: IC7.17 (V3P), JP119.1 (A), JP125.1 (A), JP132.1 (A)
WARNF: IC7.29 (WARNOUT)
~CSF: IC7.37 (~CS)

Notes on the sheet:
Référence tension
Mesure courant
