mosfet05/Metering_Unit/Kicad/Sub_Power.kicad_sch

## KiCad design Kicad/Sub_Power.kicad_sch (2025-03-12)

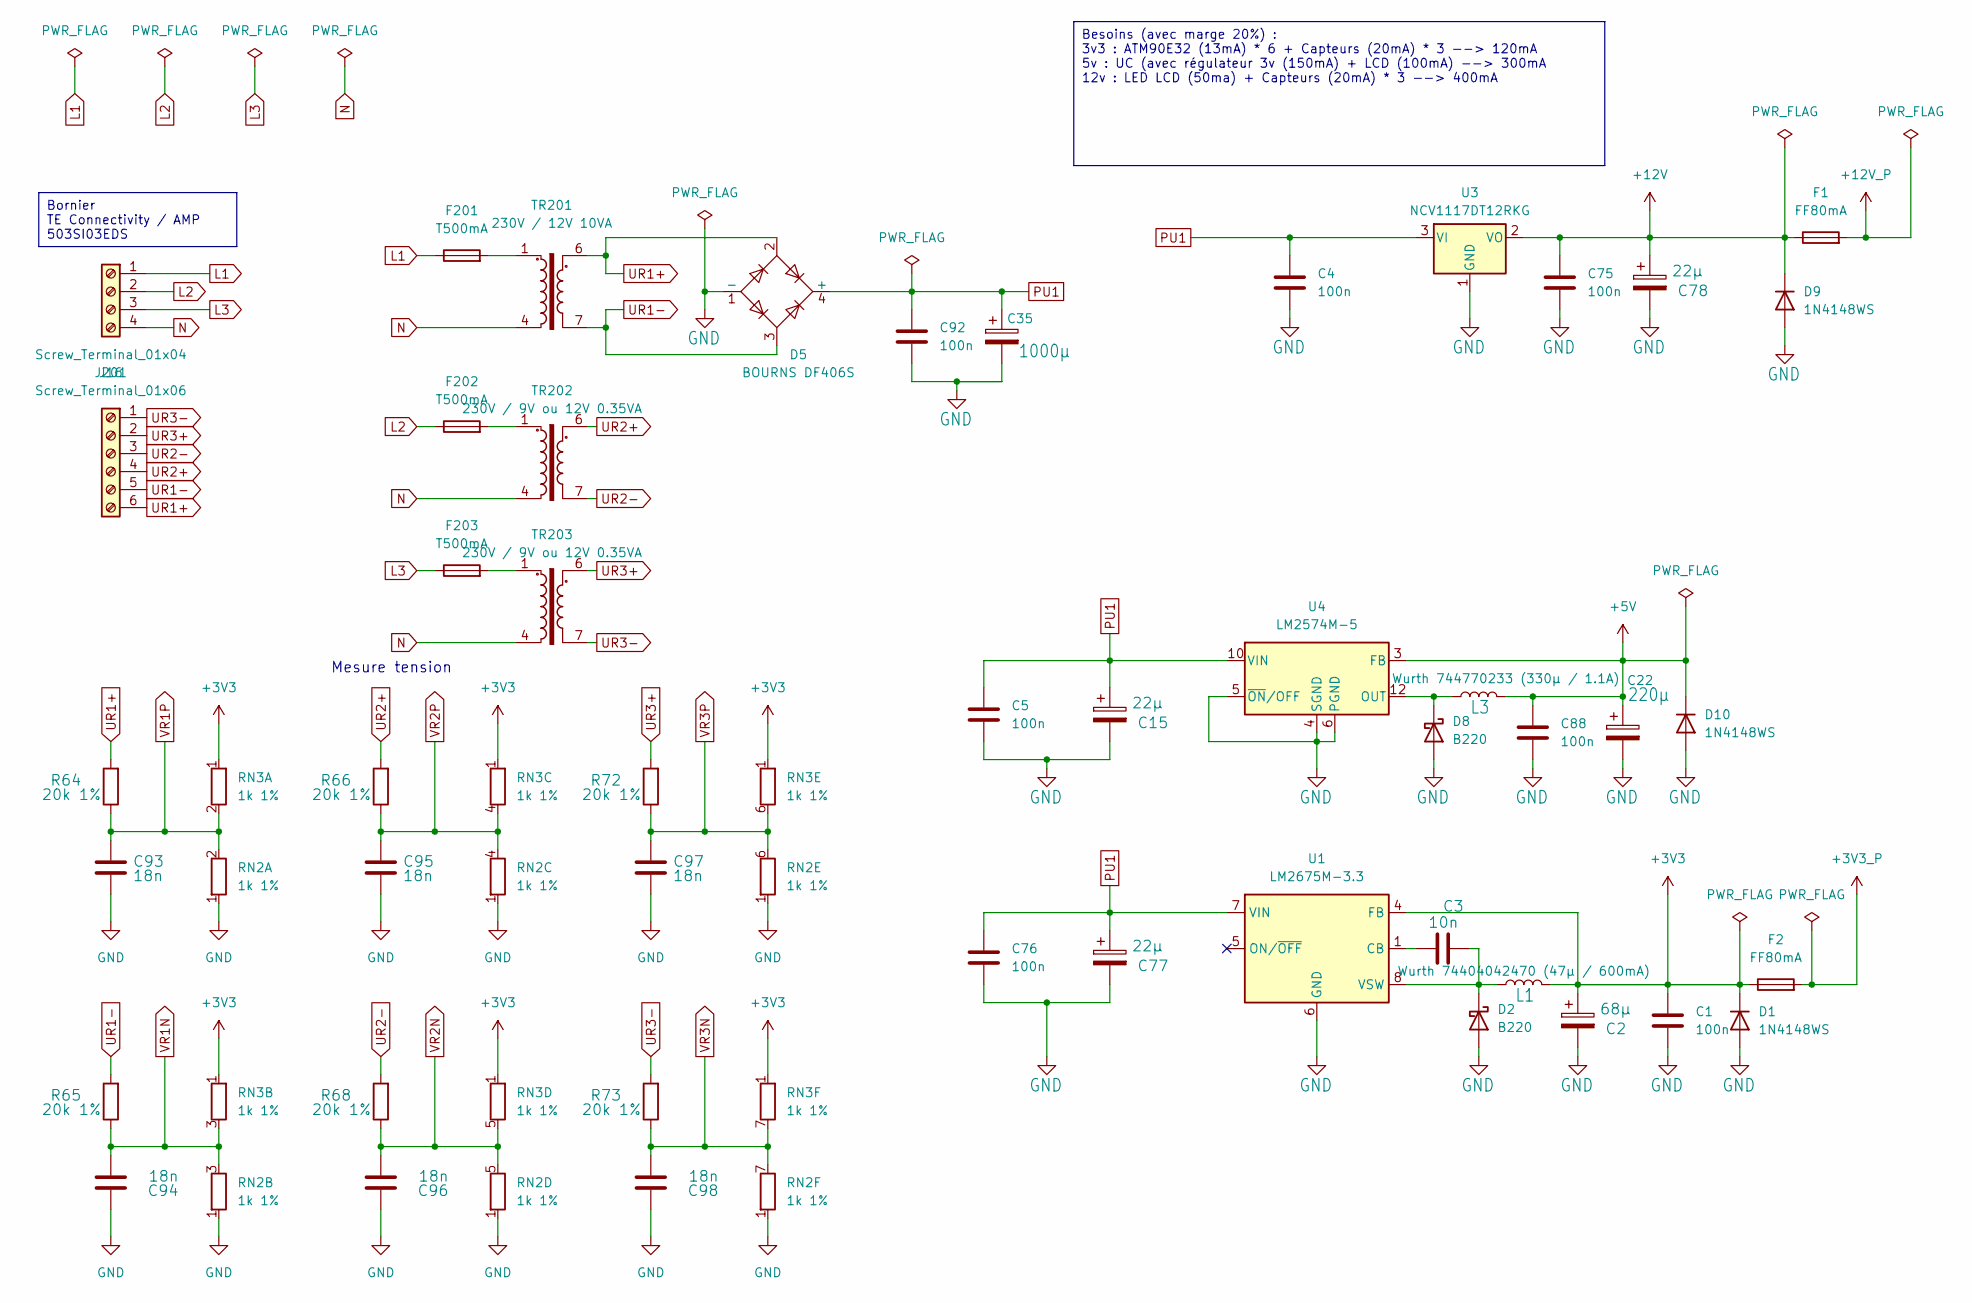
[picture p24: schematic Sub_Power.kicad_sch]

Parts:
C1, C4, C5, C75, C76, C88, C92: 100n; C_1812_4532Metric_Pad1.57x3.40mm_HandSolder
C2: 68µ; CP_Elec_6.3x5.8
C3: 10n; C_0805_2012Metric_Pad1.18x1.45mm_HandSolder
C15, C77, C78: 22µ; CP_Elec_4x5.4
C22: 220µ; CP_Radial_D6.3mm_P2.50mm
C35: 1000µ; CP_Radial_D12.5mm_P5.00mm
C93, C94, C95, C96, C97, C98: 18n; C_0805_2012Metric_Pad1.18x1.45mm_HandSolder
D1, D9, D10: 1N4148WS; D_SOD-323
D2, D8: B220; D_SMB
D5: BOURNS DF406S; Diode_Bridge_Bourns_CD-DF4xxS
F1, F2: FF80mA; Fuse_Bourns_MF-RG300
F201, F202, F203: T500mA; Fuse_Littelfuse_372_D8.50mm
J16: Screw_Terminal_01x06; TerminalBlock_MetzConnect_Type101_RT01606HBWC_1x06_P5.08mm_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
J201: Screw_Terminal_01x04
L1: Wurth 74404042470 (47µ / 600mA); L_APV_ANR4018
L3: Wurth 744770233 (330µ / 1.1A); L_12x12mm_H6mm
R64, R65, R66, R68, R72, R73: 20k 1%; R_1210_3225Metric_Pad1.30x2.65mm_HandSolder
RN2, RN3: 1k 1%; R_Array_SIP7
TR201: 230V / 12V 10VA
TR202, TR203: 230V / 9V ou 12V 0.35VA; Transformer_Breve_TEZ-22x24
U1: LM2675M-3.3; SOIC-8_3.9x4.9mm_P1.27mm
U3: NCV1117DT12RKG; TO-252-2
U4: LM2574M-5; SOIC-14W_7.5x9mm_P1.27mm

Connections:
+3V3: C1.1, C2.1, D1.1 (K), F2.1, L1.2, RN3.1 (R1), U1.4 (FB)
+3V3_P: F2.2
+5V: C22.1, C88.1, D10.1 (K), L3.2, U4.3 (FB)
+12V: C75.1, C78.1, D9.1 (K), F1.1, U3.2 (VO)
+12V_P: F1.2
GND: C1.2, C2.2, C4.2, C5.2, C15.2, C22.2, C35.2, C75.2, C76.2, C77.2, C78.2, C88.2, C92.2, C93.2, C94.1, C95.2, C96.1, C97.2, C98.1, D1.2 (A), D2.2 (A), D5.1 (-), D8.2 (A), D9.2 (A), D10.2 (A), RN2.1 (R1), U1.6 (GND), U3.1 (GND), U4.4 (SGND), U4.5 (~ON/OFF), U4.6 (PGND)
L1: F201.1, J201.1
L2: F202.1, J201.2
L3: F203.1, J201.3
N: J201.4, TR201.4, TR202.4, TR203.4
unnamed: C3.1, U1.1 (CB)
unnamed: C3.2, D2.1 (K), L1.1, U1.8 (VSW)
unnamed: D8.1 (K), L3.1, U4.12 (OUT)
unnamed: F201.2, TR201.1
unnamed: F202.2, TR202.1
unnamed: F203.2, TR203.1
PU1: C4.1, C5.1, C15.1, C35.1, C76.1, C77.1, C92.1, D5.4 (+), U1.7 (VIN), U3.3 (VI), U4.10 (VIN)
UR1+: D5.2, J16.6, R64.2, TR201.6
UR1-: D5.3, J16.5, R65.2, TR201.7
UR2+: J16.4, R66.2, TR202.6
UR2-: J16.3, R68.2, TR202.7
UR3+: J16.2, R72.2, TR203.6
UR3-: J16.1, R73.2, TR203.7
VR1N: C94.2, R65.1, RN2.3 (R2.2), RN3.3 (R2.2)
VR1P: C93.1, R64.1, RN2.2 (R1.2), RN3.2 (R1.2)
VR2N: C96.2, R68.1, RN2.5 (R4.2), RN3.5 (R4.2)
VR2P: C95.1, R66.1, RN2.4 (R3.2), RN3.4 (R3.2)
VR3N: C98.2, R73.1, RN2.7 (R6.2), RN3.7 (R6.2)
VR3P: C97.1, R72.1, RN2.6 (R5.2), RN3.6 (R5.2)

Notes on the sheet:
Bornier TE Connectivity / AMP 503SI03EDS
Besoins (avec marge 20%) : 3v3 : ATM90E32 (13mA) * 6 + Capteurs (20mA) * 3 --> 120mA 5v : UC (avec régulateur 3v (150mA) + LCD (100mA) --> 300mA 12v : LED LCD (50ma) + Capteurs (20mA) * 3 --> 400mA
Mesure tension
