mosfet05/Metering_Unit/Kicad/Sub_UC.kicad_sch

## KiCad design Kicad/Sub_UC.kicad_sch (2025-04-03)

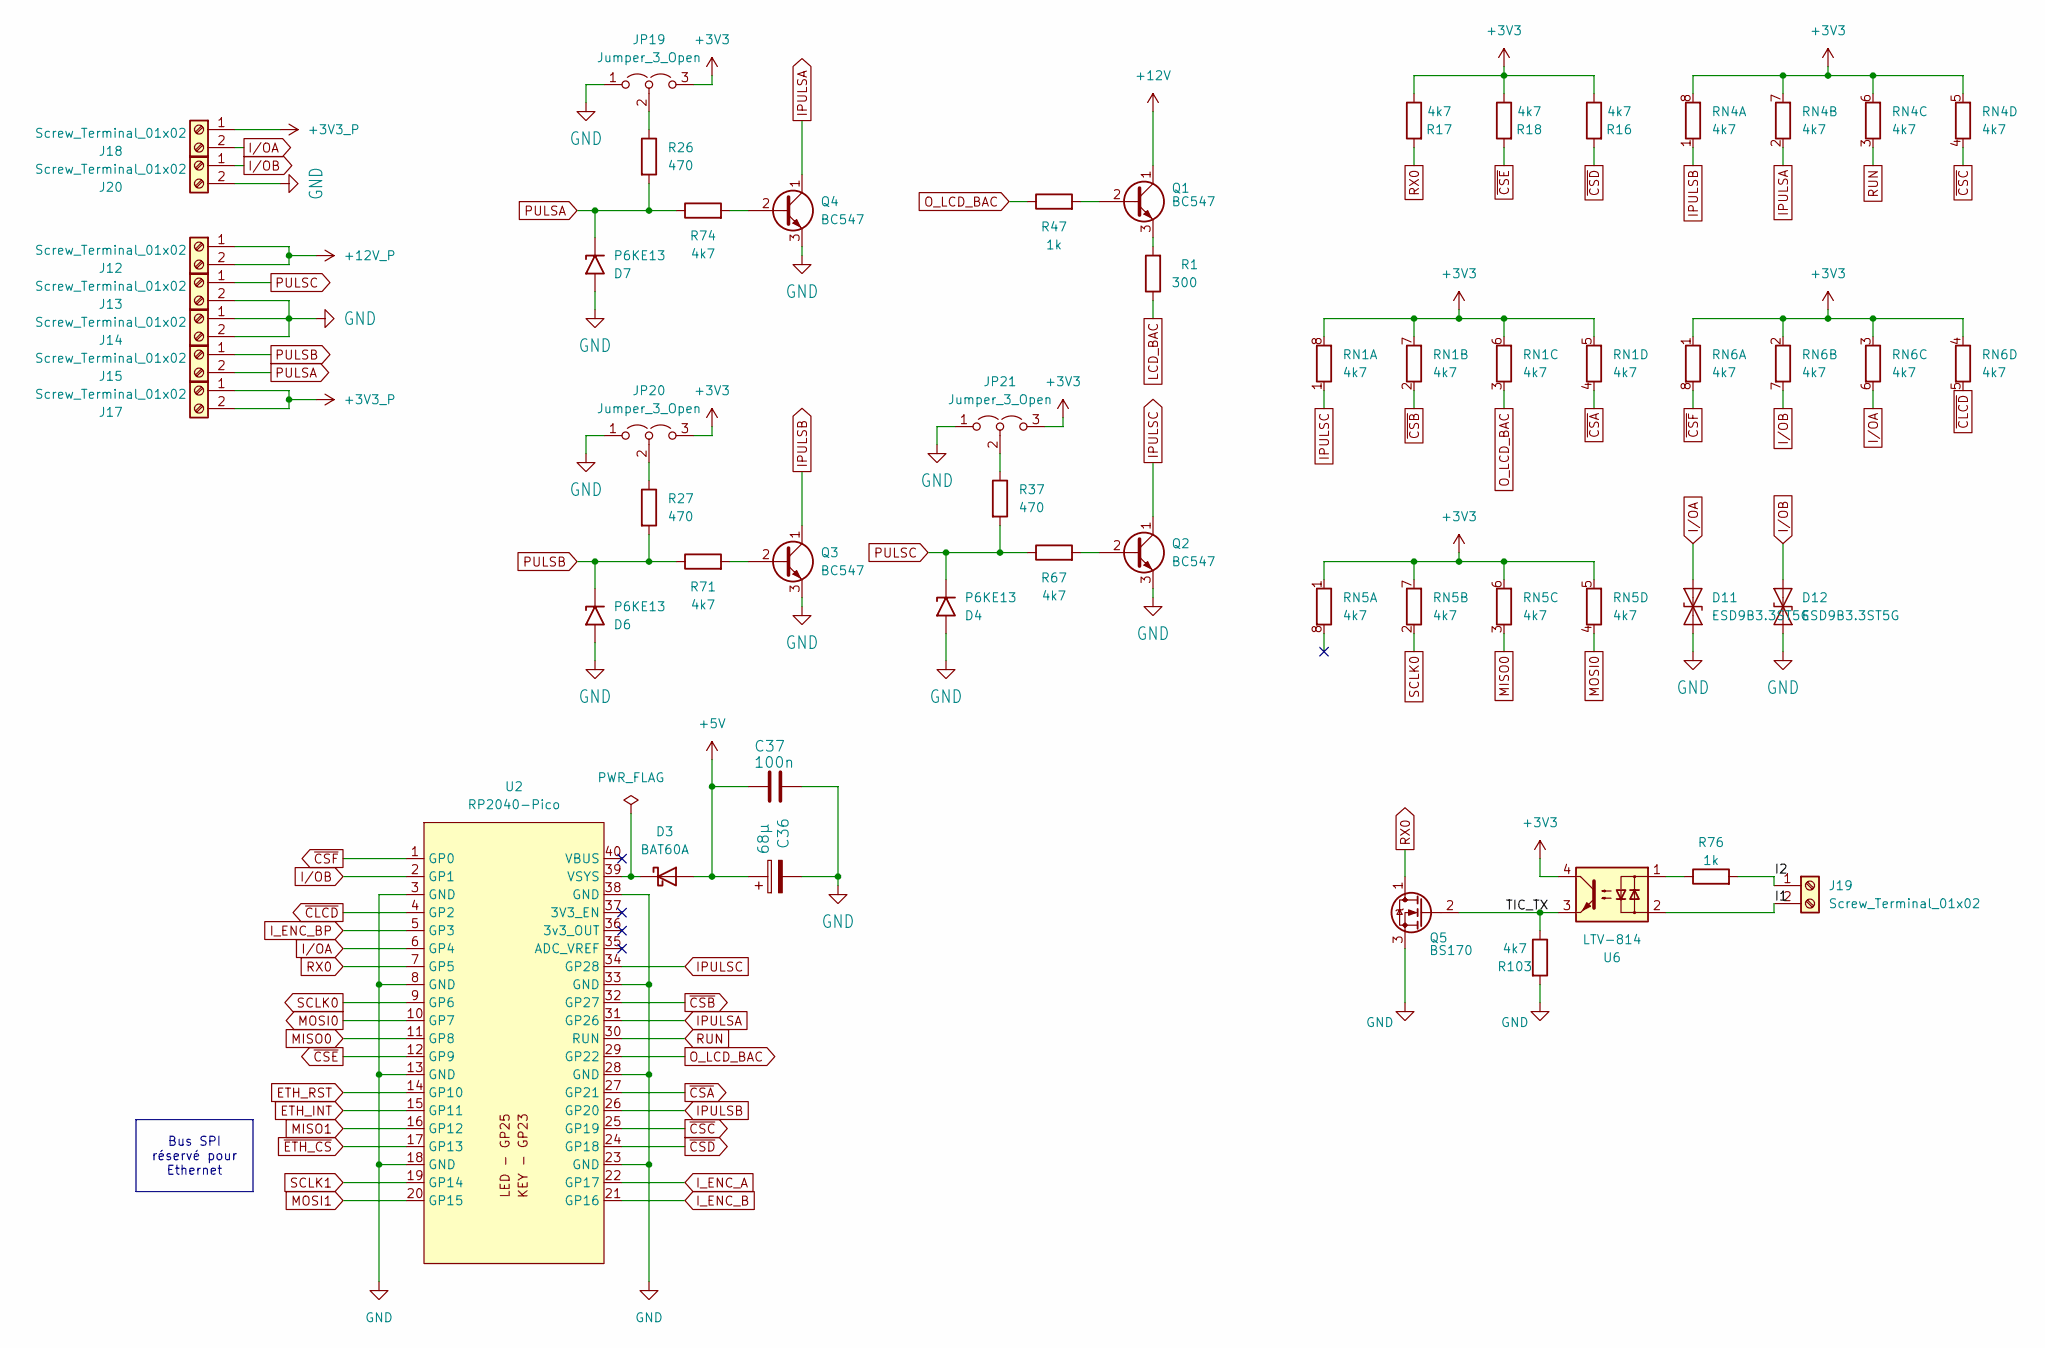
[picture p25: schematic Sub_UC.kicad_sch]

Parts:
C36: 68µ; CP_Elec_6.3x5.8
C37: 100n; C_1812_4532Metric_Pad1.57x3.40mm_HandSolder
D3: BAT60A; D_SOD-323
D4, D6, D7: P6KE13; D_DO-15_P2.54mm_Vertical_AnodeUp
D11, D12: ESD9B3.3ST5G; D_SOD-923
J12, J13, J14, J15, J17, J18, J19, J20: Screw_Terminal_01x02; TerminalBlock_VN_1x02_P2.54mm_Horizontal
JP19, JP20, JP21: Jumper_3_Open; PinHeader_1x03_P2.54mm_Vertical
Q1, Q2, Q3, Q4: BC547; TO-92_Inline
Q5: BS170; TO-92_Inline
R1: 300; R_1210_3225Metric_Pad1.30x2.65mm_HandSolder
R16, R17, R18, R67, R71, R74, R103: 4k7; R_1210_3225Metric_Pad1.30x2.65mm_HandSolder
R26, R27, R37: 470; R_1210_3225Metric_Pad1.30x2.65mm_HandSolder
R47, R76: 1k; R_1210_3225Metric_Pad1.30x2.65mm_HandSolder
RN1, RN4, RN5, RN6: 4k7; R_Array_Convex_4x1206
U2: RP2040-Pico; RP2040-Pico_CMS
U6: LTV-814; SMDIP-4_W7.62mm

Connections:
+3V3: JP19.3 (B), JP20.3 (B), JP21.3 (B), R16.1, R17.1, R18.1, RN1.5 (R4.2), RN1.6 (R3.2), RN1.7 (R2.2), RN1.8 (R1.2), RN4.5 (R4.2), RN4.6 (R3.2), RN4.7 (R2.2), RN4.8 (R1.2), RN5.1 (R1.1), RN5.5 (R4.2), RN5.6 (R3.2), RN5.7 (R2.2), RN6.1 (R1.1), RN6.2 (R2.1), RN6.3 (R3.1), RN6.4 (R4.1), U6.4
+3V3_P: J17.1, J17.2, J18.1
+5V: C36.1, C37.1, D3.2 (A)
+12V: Q1.1 (C)
+12V_P: J12.1, J12.2
ETH_INT: U2.15 (GP11)
ETH_RST: U2.14 (GP10)
GND: C36.2, C37.2, D4.2 (A2), D6.2 (A2), D7.2 (A2), D11.1 (A1), D12.1 (A1), J13.2, J14.1, J14.2, J20.2, JP19.1 (A), JP20.1 (A), JP21.1 (A), Q2.3 (E), Q3.3 (E), Q4.3 (E), Q5.3 (S), R103.2, U2.3 (GND), U2.8 (GND), U2.13 (GND), U2.18 (GND), U2.23 (GND), U2.28 (GND), U2.33 (GND), U2.38 (GND)
I1: J19.2, U6.2
I2: J19.1, R76.2
IPULSA: Q4.1 (C), RN4.2 (R2.1), U2.31 (GP26)
IPULSB: Q3.1 (C), RN4.1 (R1.1), U2.26 (GP20)
IPULSC: Q2.1 (C), RN1.1 (R1.1), U2.34 (GP28)
I_ENC_A: U2.22 (GP17)
I_ENC_B: U2.21 (GP16)
I_ENC_BP: U2.5 (GP3)
I/OA: D11.2 (A2), J18.2, RN6.6 (R3.2), U2.6 (GP4)
I/OB: D12.2 (A2), J20.1, RN6.7 (R2.2), U2.2 (GP1)
LCD_BAC: R1.1
MISO0: RN5.3 (R3.1), U2.11 (GP8)
MISO1: U2.16 (GP12)
MOSI0: RN5.4 (R4.1), U2.10 (GP7)
MOSI1: U2.20 (GP15)
unnamed: D3.1 (K), U2.39 (VSYS)
unnamed: JP19.2 (C), R26.1
unnamed: JP20.2 (C), R27.1
unnamed: JP21.2 (C), R37.1
unnamed: Q1.2 (B), R47.2
unnamed: Q1.3 (E), R1.2
unnamed: Q2.2 (B), R67.2
unnamed: Q3.2 (B), R71.2
unnamed: Q4.2 (B), R74.2
unnamed: R76.1, U6.1
O_LCD_BAC: R47.1, RN1.3 (R3.1), U2.29 (GP22)
PULSA: D7.1 (A1), J15.2, R26.2, R74.1
PULSB: D6.1 (A1), J15.1, R27.2, R71.1
PULSC: D4.1 (A1), J13.1, R37.2, R67.1
RUN: RN4.3 (R3.1), U2.30 (RUN)
RX0: Q5.1 (D), R17.2, U2.7 (GP5)
SCLK0: RN5.2 (R2.1), U2.9 (GP6)
SCLK1: U2.19 (GP14)
TIC_TX: Q5.2 (G), R103.1, U6.3
~CLCD: RN6.5 (R4.2), U2.4 (GP2)
~CSA: RN1.4 (R4.1), U2.27 (GP21)
~CSB: RN1.2 (R2.1), U2.32 (GP27)
~CSC: RN4.4 (R4.1), U2.25 (GP19)
~CSD: R16.2, U2.24 (GP18)
~CSE: R18.2, U2.12 (GP9)
~CSF: RN6.8 (R1.2), U2.1 (GP0)
~ETH_CS: U2.17 (GP13)

Notes on the sheet:
Bus SPI réservé pour Ethernet
